AidFTech/AIBus-Universal-Auto-Infotainment-System/Vehicle-Specific/Honda GA-Net II/CAN Bus Translator/PCB/BOM_9th-Gen-Civic-CANslator-BCM.csv

ID | Name | Designator | Footprint | Quantity | Manufacturer Part | Manufacturer | Supplier | Supplier Part | Price
1 | 0.1uF | C1,C2,C3,C4,C6,C7,C11,C19,C20,C31,C32,C33,C35,C36,C37,C38,C44,C51,C53,C58,C59,C60,C61,C70,C72,C78,C79,C85,C89,C91 | C0603 | 30 | 0603B104K101CT | Walsin Technology Corporation | Digi-Key | 1292-1392-1-ND
2 | 1uF | C5,C56,C57 | C0603 | 3 | CC0603KRX5R8BB105 | YAGEO | Digi-Key | 311-1445-1-ND
3 | 560pF | C8,C12,C16,C18,C21,C22,C29,C30 | C0603 | 8 | 06031C561KAT2A | AVX Corporation | Digi-Key | 478-5002-2-ND
4 | 0.1uF | C9,C15,C23,C28 | C0603 | 4 | 0603B104K101CT | Walsin Technology Corporation | Digi-Key | 1292-1392-2-ND
5 | 22pF | C10,C13,C14,C17,C24,C25,C26,C27 | C0603 | 8 | 0603N220F500CT | Walsin Technology Corporation | Digi-Key | 1292-1500-2-ND
6 | 47uF | C34,C90 | C1206 | 2 | GRM31CR61E476ME44K | Murata Electronics | Digi-Key | 490-GRM31CR61E476ME44KCT-ND
7 | 0.1u | C39,C49,C50,C75,C82 | C0603 | 5 | 06035C104JAT2A | KYOCERA AVX | Digi-Key | 478-5778-1-ND
8 | 10u | C40,C41,C48,C65,C66,C73,C74,C80,C81 | C0805 | 9 | CL21A106KAYNNNG | Samsung Electro-Mechanics | Digi-Key | 1276-6454-1-ND
9 | 22u | C42,C43,C63,C64,C76,C77,C83,C84 | C1210 | 8 | CL32B226KAJNFNE | Samsung Electro-Mechanics | Digi-Key | 1276-3391-1-ND
10 | 10u | C45 | CAP-D5.0-F2.0 | 1 | ECA-1HM100I | Panasonic Electronic Components | Digi-Key | P10425CT-ND
11 | 100n | C46,C62 | C0603 | 2 | 06035C104JAT2A | KYOCERA AVX | Digi-Key | 478-5778-1-ND
12 | 33n | C47 | C0603 | 1 | GCM188R71H333KA55D | Murata Electronics | Digi-Key | 490-8025-1-ND
13 | 1nF | C52 | C0603 | 1 | GRM1885C1H102JA01D | Murata Electronics | Digi-Key | 490-1451-1-ND
14 | 18pF | C54,C55 | C0603 | 2 | 712-QSCP251Q180J1GV001TDKR-ND | Johanson Technology Inc. | Digi-Key | 712-QSCP251Q180J1GV001TCT-ND
15 | 470pF | C67,C68 | C0603 | 2 | CL10C471JB8NNNC | Samsung Electro-Mechanics | Digi-Key | 1276-1168-1-ND
16 | 10nF | C69,C71 | C0603 | 2 | KGM15AR71H103KT | KYOCERA AVX | Digi-Key | 478-KGM15AR71H103KTCT-ND
17 | 1u | C86 | C0603 | 1 | CL10A105KB8NNNC | Samsung Electro-Mechanics | Digi-Key | 1276-1860-1-ND
18 | 2.2uF | C87,C88 | C0603 | 2 | C1608X5R1E225K080AB | TDK Corporation | Digi-Key | 445-5964-1-ND
19 | 5V | D1,D18,D24,D32 | SOD-323_L1.7-W1.3-LS2.7-RD-1 | 4 | BZT52C5V1S-TP | Micro Commercial Co | Digi-Key | BZT52C5V1S-TPMSCT-ND
20 | 3.6V | D2 | SOD-323_L1.7-W1.3-LS2.5-FD | 1 | BZX384-B3V6,115 | Nexperia USA Inc. | Digi-Key | 1727-3655-1-ND
21 | SD103AWS-TP | D3,D6,D7,D8,D9,D10,D11,D12,D13,D16,D20,D21,D22,D26,D28,D29,D30,D35 | SOD-323_L1.8-W1.3-LS2.6-FD | 18 | SD103AWS-TP | Micro Commercial Co | Digi-Key | SD103AWSTPMSCT-ND
22 | PESD1CAN-UX-ES | D4,D5,D14,D15 | SOT-323-3_L2.1-W1.3-P1.32-LS2.1-BR | 4 | PESD1CAN | EVVO | Digi-Key | 5272-PESD1CANCT-ND
23 | SK110-AQ | D17 | DO-214AC_L4.3-W2.7-LS5.2-RD | 1 | Z1SMA1 | Diotec Semiconductor | Digi-Key | 4878-Z1SMA1CT-ND
24 | SK54A-LTP | D19,D27,D31,D34 | DO-214AC_L4.3-W2.4-LS4.7-RD | 4 | SK54A-LTP | Micro Commercial Co | Digi-Key | SK54A-LTPMSCT-ND
25 | 18V | D23,D36 | SOD-123_L2.8-W1.8-LS3.7-RD | 2 | BZT52C18-7-F | Diodes Incorporated | Digi-Key | BZT52C18-FDICT-ND
26 | MBR0530-TP | D25 | SOD-123_L2.7-W1.6-LS3.7-RD-1 | 1 | MBR0530-TP | MCC (Micro Commercial Components) | Digi-Key | MBR0530TPMSCT-ND
27 | 10V | D33 | SOD-123_L2.7-W1.6-LS3.7-RD | 1 | BZT52C10-7-F | Diodes Incorporated | Digi-Key | BZT52C10-FDICT-ND
28 | 5A | F1 | FUSE-TH_01530008Z | 1 | 01530008Z | Littelfuse Inc | Digi-Key | F065-ND
29 | 15A | F2 | FUSE-TH_01530008Z | 1 | 01530008Z | Littelfuse Inc | Digi-Key | F065-ND
30 | HDR-F-2.54_1x9 | H1 | HDR-F-2.54_1X9 | 1 | RS1-09-G | Adam Tech | Digi-Key | 2057-RS1-09-G-ND
31 | 1-770967-0 | J1 | CONN-TH_1-770967-0 | 1 | 1-770967-0 | TE Connectivity(泰科电子) | Digi-Key | A32473-ND
32 | MX34020UF1 | J2 | CONN-TH_MX34020UF1 | 1 | MX34020UF1 | JAE Electronics | Digi-Key | 670-2294-ND
33 | MX34024UF1 | J3 | CONN-TH_MX34024UF1 | 1 | MX34024UF1 | JAE Electronics | Digi-Key | 670-2295-ND
34 | S02B-XASS-1(LF)(SN) | J4 | CONN-TH_P2.50_S02B-XASS-1-LF-SN | 1 | S02B-XASS-1(LF)(SN) | JST Sales America Inc. | Digi-Key | 455-S02B-XASS-1-ND
35 | B4B-XH-AM-R(LF)(SN) | J5 | CONN-TH_B4B-XH-AM-LF-SN | 1 | B4B-XH-A | JST Sales America Inc. | Digi-Key | 455-B4B-XH-A-ND
36 | 39301160 | J7 | CONN-TH_39301160 | 1 | 0039301160 | Molex | Digi-Key | WM1358-ND
37 | S06B-XASK-1(LF)(SN) | J10 | CONN-TH_5P-P2.50_S06B-XASK-1-LF-SN | 1 | S06B-XASK-1(LF)(SN) | JST Sales America Inc. | Digi-Key | 455-4091-ND
38 | PPTC032LFBN-RC | J11 | RHDR6W75P254_2X3_812X508X850P | 1 | PPTC032LFBN-RC | Sullins Connector Solutions | Digi-Key | S7071-ND
39 | 53254-0270 | J12 | MOLEX_53254-0270 | 1 | 0532540270 | Molex | Digi-Key | WM18999-ND
40 | S2B-XH-A-BK(LF)(SN) | J13,J14 | CONN-TH_S2B-XH-A-LF-SN | 2 | S2B-XH-A-BK(LF)(SN) | JST | Digi-Key | 455-S2B-XH-A-ND
41 | 0039303035 | J15 | 0039303035 FIXED | 1 | 0039303035 | Molex | Digi-Key | WM18446-ND
42 | 533750210 | J16 | CONN-TH_533750210 | 1 | 533750210 | Molex | Digi-Key | WM3421-ND
43 | 534260610 | J17 | CONN-TH_534260610 | 1 | 534260610 | Molex | Digi-Key | WM3425-ND
44 | 534260310 | J18 | CONN-TH_3P-P2.50_MOLEX_534260310 | 1 | 534260310 | Molex | Digi-Key | WM7586-ND
45 | 178495-1 | J19 | CONN-TH_178495-1 | 1 | 178495-1 | TE Connectivity AMP Connectors | Digi-Key | A106296-ND
46 | 22uH | L1,L2,L14 | IND-SMD_L6.0-W6.0_ASPI-6045S | 3 | ASPI-6045S-220M-T | Abracon LLC | Digi-Key | 535-ASPI-6045S-220M-TCT-ND
47 | 1u | L3 | L0603 | 1 | MAF1608FAD151CT000 | TDK Corporation | Digi-Key | 445-174936-1-ND
48 | 33uH | L10 | IND-SMD_L6.0-W6.0_ASPI-6045S | 1 | SPM7054VT-330M-D | TDK Corporation | Digi-Key | 445-181516-1-ND
49 | DMN67D8L-7 | Q1,Q4,Q5,Q6,Q7,Q16,Q19,Q20,Q22,Q25,Q27,Q28,Q32,Q35,Q36,Q37,Q39,Q40,Q44,Q46,Q49,Q51,Q54,Q55,Q56,Q57,Q58,Q59,Q62 | SOT-23-3_L3.0-W1.7-P0.95-LS2.9-BR | 29 | DMN67D8L-7 | Diodes Incorporated | Digi-Key | DMN67D8L-7DICT-ND
50 | DMN67D8LW-13 | Q2,Q41 | SOT-323-3_L2.2-W1.3-P1.30-LS2.1-BR | 2 | DMN67D8LW-13 | Diodes Incorporated | Digi-Key | DMN67D8LW-13DICT-ND
51 | DMP2120U-7 | Q3,Q17 | SOT-23-3_L2.9-W1.3-P1.90-LS2.4-BR | 2 | DMP2120U-7 | Diodes Incorporated | Digi-Key | DMP2120U-7DICT-ND
52 | BSS169H6327XTSA1 | Q8,Q9,Q10,Q11,Q12,Q13,Q14,Q15 | SOT-23_L2.9-W1.3-P1.90-LS2.4-BR | 8 | BSS169H6327 | Infineon Technologies | Digi-Key | BSS169H6327XTSA1CT-ND
53 | SI2347DS-T1-GE3 | Q18,Q21,Q23,Q24,Q26,Q29,Q30,Q31,Q34,Q38,Q42,Q43,Q47,Q48,Q52,Q53,Q60,Q61 | SOT-23-3_L2.9-W1.3-P1.83-LS2.4-BR-1 | 18 | SI2347DS-T1-GE3 | Vishay Siliconix | Digi-Key | SI2347DS-T1-GE3CT-ND
54 | IRF5305PBF | Q33 | TO-220F-3_L10.2-W4.7-P2.54-L | 1 | IRF5305PBF | Infineon Technologies | Digi-Key | IRF5305PBF-ND
55 | DMN3404L-7 | Q45,Q50 | SOT-23_L2.9-W1.3-P0.95-LS2.4-BR | 2 | DMN3404L-7 | Diodes Incorporated | Digi-Key | DMN3404LDICT-ND
56 | 100k | R1,R2,R3,R6,R8,R9,R11,R12,R16,R49,R50,R53,R54,R61,R62,R73,R74,R76,R86,R90,R91,R92,R127,R131,R132 | R0603 | 25 | RC0603FR-07100KL | YAGEO | Digi-Key | 311-100KHRCT-ND
57 | 10k | R4,R5,R7,R13,R15,R17,R18,R19,R20,R21,R26,R27,R28,R30,R31,R32,R33,R34,R35,R36,R37,R39,R40,R41,R46,R47,R48,R51,R52,R55,R56,R57,R58,R59,R60,R63,R66,R71,R72,R77,R78,R79,R80,R81,R82,R83,R84,R85,R87,R94,R95,R96,R97,R100,R101,R102,R103,R104,R105,R106,R107,R110,R111,R114,R115,R116,R123,R128,R129,R133 | R0603 | 70 | RNCP0603FTD10K0 | Stackpole Electronics Inc | Digi-Key | RNCP0603FTD10K0CT-ND
58 | 470 | R10,R130 | R0603 | 2 | RC0603JR-07470RL | YAGEO | Digi-Key | 311-470GRCT-ND
59 | 1M | R14 | R0603 | 1 | AC0603JR-071ML | YAGEO | Digi-Key | 311-1MLECT-ND
60 | 100 | R22,R23,R24,R25,R29,R38,R42,R43,R44,R45 | R0603 | 10 | CRCW0603100RFKEAHP | Vishay Dale | Digi-Key | 541-100STR-ND
61 | 200k | R64 | R0603 | 1 | AC0603FR-07200KL | YAGEO | Digi-Key | YAG3575CT-ND
62 | 100k | R65 | R0603 | 1 | RC0603JR-10100KL | YAGEO | Digi-Key | YAG2294CT-ND
63 | 21k | R67 | R0603 | 1 | ERJ-3EKF2102V | Panasonic Electronic Components | Digi-Key | P21.0KHCT-ND
64 | 2k | R68,R69 | R0603 | 2 | RT0603BRD072KL | YAGEO | Digi-Key | YAG1626CT-ND
65 | 10M | R70 | R0603 | 1 | RC0603FR-0710ML | YAGEO | Digi-Key | 311-10.0MHRCT-ND
66 | 12k | R75 | R0603 | 1 | RMCF0603FT12K0 | Stackpole Electronics Inc | Digi-Key | RMCF0603FT12K0CT-ND
67 | 9.76k | R88 | R0603 | 1 | RMCF0603FT9K76 | YAGEO | Digi-Key | RMCF0603FT9K76CT-ND
68 | 30.1k | R89 | R0603 | 1 | RMCF0603FT30K1 | YAGEO | Digi-Key | RMCF0603FT30K1CT-ND
69 | 0.01 | R93 | R0603 | 1 | CSM0603FT10L0 | Stackpole Electronics Inc | Digi-Key | CSM0603FT10L0CT-ND
70 | 1k | R98,R99 | R0603 | 2 | RC0603FR-071KL | YAGEO | Digi-Key | 311-1.00KHRCT-ND
71 | 9.1k | R108 | R0603 | 1 | RC0603FR-079K1L | YAGEO | Digi-Key | 311-9.10KHRCT-ND
72 | 1k | R109 | R0603 | 1 | RMCF0603FT1K00 | Stackpole Electronics Inc | Digi-Key | RMCF0603FT1K00CT-ND
73 | 0 | R112,R113 | R0603 | 2 | RC0603JR-070RL | YAGEO | Digi-Key | 311-0.0GRCT-ND
74 | 27 | R117,R118,R119,R120,R121,R122 | R0603 | 6 | RC0603FR-0727RL | YAGEO | Digi-Key | 311-27.0HRCT-ND
75 | 3k | R124 | R0603 | 1 | RT0603BRD073KL | YAGEO | Digi-Key | YAG1657CT-ND
76 | 47k | R125 | R0603 | 1 | RG1608P-473-B-T5 | Susumu | Digi-Key | RG16P47.0KBCT-ND
77 | 16k | R126 | R0603 | 1 | RT0603BRD0716KL | YAGEO | Digi-Key | YAG1546CT-ND
78 | ATMEGA4808-AUR | U1 | TQFP-32_L7.0-W7.0-P0.80-LS9.0-BL | 1 | ATMEGA4808-AUR | Microchip Technology | Digi-Key | 150-ATMEGA4808-AURCT-ND
79 | AP331AWG-7 | U2,U22 | SOT-25-5_L3.0-W1.8-P0.95-LS3.0-BR | 2 | AP331AWG-7 | Diodes Incorporated | Digi-Key | AP331AWGDICT-ND
80 | MCP2561T-E/SN | U3,U6,U9,U10,U13 | SOIC-8_L4.9-W3.9-P1.27-LS6.0-BL-2 | 5 | MCP2561T-E/SN | Microchip Technology | Digi-Key | MCP2561T-E/SNCT-ND
81 | SN74LVC1G14DBVR-MS | U5 | SOT-23-5_L3.0-W1.7-P0.95-LS2.8-BR | 1 | SN74LVC1G14DBVR-MS | Texas Instruments | Digi-Key | 296-11607-1-ND
82 | MCP2515T-I/SO | U7,U8,U11,U12 | SOIC-18_L11.6-W7.5-P1.27-LS10.3-BL | 4 | MCP2515T-I/SO | Microchip Technology | Digi-Key | MCP2515T-I/SOTR-ND
83 | ADG752BRTZ-REEL7 | U15 | SOT-23-6_L2.9-W1.6-P0.95-LS2.8-BL | 1 | ADG752BRTZ-REEL7 | Analog Devices Inc. | Digi-Key | 505-ADG752BRTZ-REEL7CT-ND
84 | MCP23S08-E/SO | U16,U18,U28 | SOIC-18_L11.6-W7.5-P1.27-LS10.3-BL | 3 | MCP23S08-E/SO | Microchip Technology | Digi-Key | MCP23S08-E/SO-ND
85 | MCP3201T-CI/SN | U17,U32 | SOIC-8_L4.9-W3.9-P1.27-LS6.0-BL | 2 | MCP3201T-CI/SN | Microchip Technology | Digi-Key | MCP3201T-CI/SNCT-ND
86 | AP63301WU-7 | U19,U27,U30 | TSOT-23-6_L2.9-W1.6-P0.95-LS2.8-BR | 3 | AP63301WU-7 | Diodes Incorporated | Digi-Key | AP63301WU-7
87 | AP7375-33SA-7 | U20 | SOT-23-3_L2.9-W1.3-P1.90-LS2.4-BR | 1 | AP7375-33SA-7 | Diodes Incorporated | Digi-Key | 31-AP7375-33SA-7CT-ND
88 | USB2513BI-AEZG | U21 | QFN-36_L6.0-W6.0-P0.50-BL-EP | 1 | USB2513BI-AEZG | Microchip Technology | Digi-Key | USB2513B-AEZC-ND
89 | NCS214RSQT2G | U23 | SC-70-6_L2.0-W1.3-P0.65-LS2.1-BL | 1 | NCS214RSQT2G | onsemi | Digi-Key | NCS214RSQT2GOSCT-ND
90 | LM2596T-ADJ/NOPB | U24 | TO-220-5_L10.5-W15.5-P1.70-TL | 1 | LM2596T-ADJ/NOPB | Texas Instruments | Digi-Key | LM2596T-ADJ/NOPB-ND
91 | NA556 | U25 | SOIC-14_L8.7-W3.9-P1.27-LS6.0-BL | 1 | NA556DR | Texas Instruments | Digi-Key | 296-21754-1-ND
92 | MCP4251-104E/SL | U26 | SOIC-14_L8.7-W3.9-P1.27-LS6.0-BL | 1 | MCP4251-104E/SL | Microchip Technology | Digi-Key | MCP4251-104E/SL-ND
93 | SN74LVC2G04DBVR | U29 | SOT-23-6_L2.9-W1.6-P0.95-LS2.8-BR | 1 | SN74LVC2G04DBVR | Texas Instruments | Digi-Key | 296-13261-1-ND
94 | LM2776DBVT | U31 | SOT-23-6_L2.9-W1.6-P0.95-LS2.8-BR | 1 | LM2776DBVT | Texas Instruments | Digi-Key | 296-42300-1-ND
95 | USB-A2VSW6 | USB1 | USB-A-TH_USB-A2VSW6 | 1 | USB-A2VSW6 | On-Shore Technology, Inc. | Digi-Key | On Shore Technology Inc.
96 | USB-A1HSW6 | USB2 | USB-A-TH_USB-A1HSW6 | 1 | USB-A1HSW6 | On Shore Technology Inc. | Digi-Key | ED2989-ND
97 | UJ2-BH-BL1-TH | USB3 | USB-B-TH_GT-USB-2014-CWG1 | 1 | UJ2-BH-BL1-TH | Same Sky (Formerly CUI Devices) | Digi-Key | 102-3999-ND
98 | 16MHz | X1,X2,X3,X4 | HC-49US-SMD_L7.0-W4.1 | 4 | ECS-160-20-3X-EN-TR | ECS Inc. | Digi-Key | XC1793CT-ND
99 | 24MHz | X5 | CRYSTAL-SMD_4P-L2.0-W1.6-BL-B | 1 | XRCGB24M000F3M00R0 | Murata Electronics | Digi-Key | 490-5576-1-ND
100 | TL061IDT | U4,U14 | SOIC-8_L4.9-W3.9-P1.27-LS6.2-BL | 2 | TL061IDT | STMicroelectronics | Digi-Key | 497-4054-1-ND
