AidFTech/AIBus-Universal-Auto-Infotainment-System/Vehicle-Specific/Honda GA-Net II/Audio Source Translator/PCB/BOM_Honda-GA-Net-Translator.csv

ID | Name | Designator | Footprint | Quantity | Manufacturer Part | Manufacturer | Supplier | Supplier Part | Price
1 | 0.1uF | C1,C6,C7,C8,C9,C11,C14,C15,C16,C17,C18,C19,C20,C21,C22,C23,C24,C25,C26,C27,C28,C29,C30,C31,C32,C34,C36,C37,C38,C39,C42,C43,C52,C55,C73 | C0603 | 35 | 0603B104K101CT | Walsin Technology Corporation | Digi-Key | 1292-1392-1-ND
2 | 33n | C2 | C0603 | 1 | GCM188R71H333KA55D | Murata Electronics | Digi-Key | 490-8025-1-ND
3 | 100n | C3 | C0603 | 1 | 06035C104JAT2A | KYOCERA AVX | Digi-Key | 478-5778-1-ND
4 | 10u | C4 | CAP-D5.0-F2.0 | 1 | ECA-1HM100I | Panasonic Electronic Components | Digi-Key | P10425CT-ND
5 | 1uF | C5,C53,C54 | C0603 | 3 | CC0603KRX5R8BB105 | YAGEO | Digi-Key | 311-1445-1-ND
6 | 100u | C10 | CAP-D6.3×F2.5 | 1 | ESK107M025AE3EA | KEMET | Digi-Key | 399-6650-1-ND
7 | 22pF | C12,C13 | C0603 | 2 | 0603N220F500CT | Walsin Technology Corporation | Digi-Key | 1292-1500-2-ND
8 | 10n | C33,C35,C101 | C0603 | 3 | GCM188R72A103KA37D | Murata Electronics | Digi-Key | 490-4781-1-ND
9 | 10nF | C40 | C0603 | 1 | KGM15AR71H103KT | KYOCERA AVX | Digi-Key | 478-KGM15AR71H103KTCT-ND
10 | 470pF | C41 | C0603 | 1 | CL10C471JB8NNNC | Samsung Electro-Mechanics | Digi-Key | 1276-1168-1-ND
11 | 22u | C45,C46,C57,C58,C59,C60,C67,C68 | C1210 | 8 | CL32B226KAJNFNE | Samsung Electro-Mechanics | Digi-Key | 1276-3391-1-ND
12 | 0.1u | C47,C56,C61,C66 | C0603 | 4 | 06035C104JAT2A | KYOCERA AVX | Digi-Key | 478-5778-1-ND
13 | 10u | C48,C49,C50,C51,C62,C63,C64,C65 | C0805 | 8 | CL21A106KAYNNNG | Samsung Electro-Mechanics | Digi-Key | 1276-6454-1-ND
14 | 5.6V | D1 | SOD-123_L2.7-W1.6-LS3.7-RD-A | 1 | MMSZ5232BT1G | onsemi | Digi-Key | MMSZ5232BT1GOSCT-ND
15 | 3.6V | D2,D10 | SOD-123_L2.7-W1.6-LS3.7-RD-A | 2 | MMSZ4685-TP | Micro Commercial Co | Digi-Key | MMSZ4685-TPMSCT-ND
16 | 6.8V | D3,D4 | SOD-123_L2.7-W1.6-LS3.7-RD-A | 2 | MMSZ4692T1G | onsemi | Digi-Key | MMSZ4692T1GOSCT-ND
17 | POWER | D5 | LED-TH_BD5.0-P2.54-FD | 1 | LTL-4233 | Lite-On Inc. | Digi-Key | 160-1130-ND
18 | ACTIVITY | D6 | LED-TH_BD5.0-P2.54-FD | 1 | LTL-4273 | Lite-On Inc. | Digi-Key | 160-1966-ND
19 | SD103AWS-TP | D7,D8,D9,D11,D13,D15,D17,D19,D22,D23,D24,D25,D27 | SOD-323_L1.8-W1.3-LS2.6-FD | 13 | SD103AWS-TP | Micro Commercial Co | Digi-Key | SD103AWSTPMSCT-ND
20 | SK54A-LTP | D12,D14,D16,D18 | DO-214AC_L4.3-W2.4-LS4.7-RD | 4 | SK54A-LTP | Micro Commercial Co | Digi-Key | SK54A-LTPMSCT-ND
21 | 3.6V | D20 | SOD-323_L1.7-W1.3-LS2.5-FD | 1 | BZX384-B3V6,115 | Nexperia USA Inc. | Digi-Key | 1727-3655-1-ND
22 | 5V | D21 | SOD-323_L1.7-W1.3-LS2.7-RD-1 | 1 | BZT52C5V1S-TP | Micro Commercial Co | Digi-Key | BZT52C5V1S-TPMSCT-ND
23 | PROG | D26 | LED0805-RD | 1 | LTST-C171KGKT | Lite-On Inc. | Digi-Key | 160-1426-1-ND
24 | S08B-XADSS-N | J1,J2 | CONN-TH_8P-P2.50_S08B-XADSS-N-LF-SN | 2 | S08B-XADSS-N | JST Sales America Inc. | Digi-Key | 455-S08B-XADSS-N-ND
25 | MX34012NF1_C9900019510 | J3 | CONN-TH_MX34012NF1 | 1 | MX34012NF1 | JAE Electronics | Digi-Key | 670-2285-ND
26 | 53254-0270 | J4 | MOLEX_53254-0270 | 1 | 0532540270 | Molex | Digi-Key | WM18999-ND
27 | HDR-M-2.54_1x8 | J5 | HDR-M-2.54_2X4 | 1 | TSW-104-07-F-D | Samtec Inc. | Digi-Key | SAM8996-ND
28 | 0559350310 | J6 | 0559350310 | 1 | 0559350310 | Molex | Digi-Key | WM12297-ND
29 | 1u | L1,L2,L3,L4,L5,L6,L7,L8,L9 | L0603 | 9 | MAF1608FAD151CT000 | TDK Corporation | Digi-Key | 445-174936-1-ND
30 | 22uH | L12,L13,L14,L15 | IND-SMD_L6.0-W6.0_ASPI-6045S | 4 | ASPI-6045S-220M-T | Abracon LLC | Digi-Key | 535-ASPI-6045S-220M-TCT-ND
31 | DMN67D8L-7 | Q1,Q4,Q6,Q8,Q9 | SOT-23-3_L3.0-W1.7-P0.95-LS2.9-BR | 5 | DMN67D8L-7 | Diodes Incorporated | Digi-Key | DMN67D8L-7DICT-ND
32 | DMN67D8LW-13 | Q2,Q14,Q16,Q18,Q19,Q20,Q21 | SOT-323-3_L2.2-W1.3-P1.30-LS2.1-BR | 7 | DMN67D8LW-13 | Diodes Incorporated | Digi-Key | DMN67D8LW-13DICT-ND
33 | DMP2120U-7 | Q3 | SOT-23-3_L2.9-W1.3-P1.90-LS2.4-BR | 1 | DMP2120U-7 | Diodes Incorporated | Digi-Key | DMP2120U-7DICT-ND
34 | SI2347DS-T1-GE3 | Q5,Q15 | SOT-23-3_L2.9-W1.3-P1.83-LS2.4-BR-1 | 2 | SI2347DS-T1-GE3 | Vishay Siliconix | Digi-Key | SI2347DS-T1-GE3CT-ND
35 | IRF5305PBF | Q7 | TO-220F-3_L10.2-W4.7-P2.54-L | 1 | IRF5305PBF | Infineon Technologies | Digi-Key | IRF5305PBF-ND
36 | 2N7002 | Q17 | SOT-23_L2.9-W1.3-P0.95-LS2.4-BR | 1 | DMN3404L-7 | Diodes Incorporated | Digi-Key | DMN3404LDICT-ND
37 | 10k | R1,R2,R4,R5,R7,R8,R9,R12,R16,R17,R20,R21,R22,R23,R24,R25,R26,R27,R28,R29,R31,R33,R40,R41,R43,R44,R46,R55,R63,R64,R70,R83 | R0603 | 32 | RNCP0603FTD10K0 | Stackpole Electronics Inc | Digi-Key | RNCP0603FTD10K0CT-ND
38 | 47k | R3,R6,R32,R34 | R0603 | 4 | RC0603FR-0747KL | YAGEO | Digi-Key | 311-47.0KHRCT-ND
39 | 100k | R10,R11,R18,R19,R56,R57,R59,R60,R61,R62,R65,R66,R67,R68 | R0603 | 14 | RC0603FR-07100KL | YAGEO | Digi-Key | 311-100KHRCT-ND
40 | 270 | R13,R14,R45 | R0805 | 3 |  |  | Digi-Key | 311-270ARCT-ND
41 | 100 | R15 | R0805 | 1 |  |  | Digi-Key | A126416CT-ND
42 | 2.2k | R30 | R0603 | 1 | RMCF0603FT2K20 | Stackpole Electronics Inc | Digi-Key | RMCF0603FT2K20CT-ND
43 | 1k | R35,R42 | R0603 | 2 | RC0603FR-071KL | YAGEO | Digi-Key | 311-1.00KHRCT-ND
44 | 20k | R36,R48 | R0603 | 2 | RT0603BRD0720KL | YAGEO | Digi-Key | YAG1582CT-ND
45 | 130k | R37,R47 | R0603 | 2 | RT0603BRD07130KL | YAGEO | Digi-Key | YAG1521CT-ND
46 | 150 | R38,R39,R71 | R0603 | 3 | RC0603FR-07150RL | YAGEO | Digi-Key | 311-150HRCT-ND
47 | 16k | R49 | R0603 | 1 | RT0603BRD0716KL | YAGEO | Digi-Key | YAG1546CT-ND
48 | 47k | R50 | R0603 | 1 | RG1608P-473-B-T5 | Susumu | Digi-Key | RG16P47.0KBCT-ND
49 | 3k | R51 | R0603 | 1 | RT0603BRD073KL | YAGEO | Digi-Key | YAG1657CT-ND
50 | 2k | R52,R53 | R0603 | 2 | RT0603BRD072KL | YAGEO | Digi-Key | YAG1626CT-ND
51 | 21k | R54 | R0603 | 1 | ERJ-3EKF2102V | Panasonic Electronic Components | Digi-Key | P21.0KHCT-ND
52 | 1M | R58 | R0603 | 1 | AC0603JR-071ML | YAGEO | Digi-Key | 311-1MLECT-ND
53 | 10M | R69 | R0603 | 1 | RC0603FR-0710ML | YAGEO | Digi-Key | 311-10.0MHRCT-ND
54 | 270 | R85,R86 | R0603 | 2 | RC0603FR-07270RL | YAGEO | Digi-Key | 311-270HRCT-ND
55 | OS102011MS2QN1 | SW1 | SW-TH_OS102011MS2QN1 | 1 | OS102011MS2QN1 | C&K | Digi-Key | CKN9565-ND
56 | ATMEGA1280-16AU | U1 | ATMEGA2560-16AU | 1 | ATMEGA1280-16AU | Microchip Technology | Digi-Key | ATMEGA1280-16AU-ND
57 | MCP2561T-E/SN | U2,U5,U7 | SOIC-8_L4.9-W3.9-P1.27-LS6.0-BL-2 | 3 | MCP2561T-E/SN | Microchip Technology | Digi-Key | MCP2561T-E/SNCT-ND
58 | SN74LVC1G14DBVR-MS | U3 | SOT-23-5_L3.0-W1.7-P0.95-LS2.8-BR | 1 | SN74LVC1G14DBVR-MS | Texas Instruments | Digi-Key | 296-11607-1-ND
59 | 11.2896MHZ | U4 | OSC-SMD_4P-L2.5-W2.0-BL-1 | 1 | KC2520Z11.2896C1KX00 | KYOCERA AVX | Digi-Key | 478-KC2520Z11.2896C1KX00CT-ND
60 | MCP6006UT-E/OT | U10 | SOT-23-5_L3.0-W1.6-P0.95-LS2.8-BL | 1 | MCP6006UT-E/OT | Microchip Technology | Digi-Key | 150-MCP6006UT-E/OTCT-ND
61 | SN74LVC2G14DCKR(UMW) | U11 | SC-70-6_L2.0-W1.3-P0.65-LS2.2-BL | 1 | SN74LVC2G14DCKR | Texas Instruments | Digi-Key | 296-13011-1-ND
62 | SN74LVC2G00DCTR | U12 | SSOP-8_L3.0-W2.8-P0.65-LS4.0-BL-1 | 1 | SN74LVC2G00DCTR | Texas Instruments | Digi-Key | 296-13257-1-ND
63 | SN74LVC1G08DCKR | U13 | SC-70-5_L2.1-W1.3-P0.65-LS2.1-BR | 1 | SN74LVC1G08DCKR | Texas Instruments | Digi-Key | 296-11602-1-ND
64 | DIT4096IPWR | U14 | SSOP-28 | 1 | DIT4096IPWR | Texas Instruments | Digi-Key | 296-DIT4096IPWRCT-ND
65 | 74HCT123D,652 | U15 | SOIC-16_L9.9-W3.9-P1.27-LS6.0-BL | 1 | 74HCT123D,653 | Nexperia USA Inc. | Digi-Key | 1727-7300-1-ND
66 | SN74LVC1G14DBVR_C434069 | U16 | SOT-23-5_L3.0-W1.7-P0.95-LS2.8-BR | 1 | SN74LVC1G14DBVR | Texas Instruments | Digi-Key | 296-11607-1-ND
67 | SN74HC595DRG4 | U17,U18 | SOIC-16_L9.9-W3.9-P1.27-LS6.0-BL | 2 | SN74HC595DR | Texas Instruments | Digi-Key | 296-14857-1-ND
68 | CD4029BM | U19 | SOIC-16_L9.9-W3.9-P1.27-LS6.0-BL | 1 | CD4029BM96 | Texas Instruments | Digi-Key | 296-38054-1-ND
69 | MCP4251-104E/SL | U20 | SOIC-14_L8.7-W3.9-P1.27-LS6.0-BL | 1 | MCP4251-104E/SL | Microchip Technology | Digi-Key | MCP4251-104E/SL-ND
70 | PCM1808PWR | U21 | TSSOP-14_L5.0-W4.4-P0.65-LS6.4-BL | 1 | PCM1808PWR | Texas Instruments | Digi-Key | 296-26307-1-ND
71 | NE555DR-CN | U22 | SOP-8_L5.0-W4.0-P1.27-LS6.0-BL | 1 | NE555DR-CN | Texas Instruments | Digi-Key | 296-6501-1-ND
72 | AP331AWG-7 | U23 | SOT-25-5_L3.0-W1.8-P0.95-LS3.0-BR | 1 | AP331AWG-7 | Diodes Incorporated | Digi-Key | AP331AWGDICT-ND
73 | D-AS321KTR-G1 | U24 | SOT-23-5_L2.9-W1.6-P0.95-LS2.8-BL | 1 | AS321KTR-G1 | Diodes Incorporated | Digi-Key | AS321KTR-G1DICT-ND
74 | AP63301WU-7 | U25,U26 | TSOT-23-6_L2.9-W1.6-P0.95-LS2.8-BR | 2 | AP63301WU-7 | DIODES(美台) | Digi-Key | AP63301WU-7
75 | AP63301WU-7 | U27,U28 | TSOT-23-6_L2.9-W1.6-P0.95-LS2.8-BR | 2 | AP63301WU-7 | Diodes Incorporated | Digi-Key | AP63301WU-7
76 | TC4W66FU,LF | U30 | SSOP-8_L2.9-W2.8-P0.65-LS4.0-BL | 1 | TC4W66FU,LF | Toshiba Semiconductor and Storage | Digi-Key | TC4W66FULFCT-ND
77 | 16MHz | X1 | HC-49US-SMD_L7.0-W4.1 | 1 | ECS-160-20-3X-EN-TR | ECS Inc. | Digi-Key | XC1793CT-ND
78 | TL061IDT | U6 | SOIC-8_L4.9-W3.9-P1.27-LS6.2-BL | 1 | TL061IDT | STMicroelectronics | Digi-Key | 497-4054-1-ND
79 | LM2904BAQDRQ1 | U8 | SOIC-8_L4.9-W3.9-P1.27-LS6.0-BL | 1 | LM2904BIDR | Texas Instruments | Digi-Key | 296-LM2904BIDRCT-ND
80 | TL072IDR(UMW) | U9 | SOIC-8_L4.9-W3.9-P1.27-LS6.0-BL | 1 | TL072IDR | Texas Instruments | Digi-Key | 296-7194-1-ND
81 | LM6172IM | U29 | SOIC-8_L5.0-W4.0-P1.27-LS6.0-BL | 1 | LM6172IMX/NOPB | Texas Instruments | Digi-Key | LM6172IMX/NOPBCT-ND
