AidFTech/AIBus-Universal-Auto-Infotainment-System/Vehicle-Specific/Honda GA-Net II/2006-2011 Navigation Screen/PCB/BOM_8th-gen-Civic-Navigation-Screen-AIBT-Front.csv

ID | Name | Designator | Footprint | Quantity | Manufacturer Part | Manufacturer | Supplier | Supplier Part | Price
1 | 10k | R21,R17,R18,R19,R16,R14,R15,R13,R9,R10,R6,R7,R8,R1,R2,R4 | R0603 | 16 | RNCP0603FTD10K0 | Stackpole Electronics Inc | Digi-Key | RNCP0603FTD10K0CT-ND
2 | SD103AWS-TP | D7,D6 | SOD-323_L1.8-W1.3-LS2.6-FD | 2 | SD103AWS-TP | Micro Commercial Co | Digi-Key | SD103AWSTPMSCT-ND
3 | SI2347DS-T1-GE3 | Q11 | SOT-23-3_L2.9-W1.3-P1.83-LS2.4-BR-1 | 1 | SI2347DS-T1-GE3 | Vishay Siliconix | Digi-Key | SI2347DS-T1-GE3CT-ND
4 | DMN67D8LW-13 | Q12,Q1,Q3,Q4,Q6,Q10 | SOT-23_L2.9-W1.3-P0.95-LS2.4-BR | 6 | DMN67D8LW-13 | Diodes Incorporated | Digi-Key | DMN67D8LW-13DICT-ND
5 | 12k | R20 | R0603 | 1 | RMCF0603FT12K0 | Stackpole Electronics Inc | Digi-Key | RMCF0603FT12K0CT-ND
6 | LM393PSRG4 | U17 | SOIC-8_L6.2-W5.3-P1.27-LS8.0-BL | 1 | LM393DR | Texas Instruments | Digi-Key | 296-1015-1-ND
7 | SN74LVC1G08DBVR | U18 | SOT-23-5_L3.0-W1.7-P0.95-LS2.8-BR | 1 | SN74LVC1G08DBVR | Texas Instruments | Digi-Key | 296-11601-1-ND
8 | 100n | C32,C27,C28,C29,C30,C31,C1,C2,C3,C7,C12,C20,C21,C22,C25,C26 | C0603 | 16 | 06035C104JAT2A | KYOCERA AVX | Digi-Key | 478-5778-1-ND
9 | CD40107BM96 | U15 | SOIC-8_L4.9-W3.9-P1.27-LS6.0-BL | 1 | CD40107BM96 | Texas Instruments | Digi-Key | 296-31481-1-ND
10 | SN74LVC2G14DCKR_C19829677 | U16,U10 | SOT-363_L2.1-W1.3-P0.65-LS2.2-BL | 2 | SN74LVC2G14DCKR | Texas Instruments | Digi-Key | 296-13011-1-ND
11 | CD4029BM | U11,U13 | SOIC-16_L9.9-W3.9-P1.27-LS6.0-BL | 2 | CD4029BM96 | Texas Instruments | Digi-Key | 296-38054-1-ND
12 | MCP23S08-E/SO | U12,U2,U3,U4 | SOIC-18_L11.6-W7.5-P1.27-LS10.3-BL | 4 | MCP23S08-E/SO | Microchip Technology | Digi-Key | MCP23S08-E/SO-ND
13 | SN74LVC1G32DCKRE4 | U14 | SC-70-5_L2.0-W1.3-P0.65-LS2.1-BR | 1 | SN74LVC1G32DCKR | Texas Instruments | Digi-Key | 296-9848-1-ND
14 | 22pF | C4,C5 | C0603 | 2 | 0603N220F500CT | Walsin Technology Corporation | Digi-Key | 1292-1500-2-ND
15 | 0.1uF | C6 | C0603 | 1 | 0603B104K101CT | Walsin Technology Corporation | Digi-Key | 1292-1392-2-ND
16 | 0.1u | C13 | C0603 | 1 | 06035C104JAT2A | KYOCERA AVX | Digi-Key | 478-5778-1-ND
17 | 10n | C23,C24 | C0603 | 2 | GCM188R72A103KA37D | Murata Electronics | Digi-Key | 490-4781-1-ND
18 | 62684-502100AHLF | FPC2 | 62684-502100AHLF | 1 | 62684-502100AHLF | Amphenol ICC (FCI) | Digi-Key | 609-62684-502100AHLFCT-ND
19 | 100k | R11,R12 | R0603 | 2 | RC0603FR-07100KL | YAGEO | Digi-Key | 311-100KHRCT-ND
20 | SN74LVC2G74DCURE4 | U8 | VSSOP-8_L2.3-W2.0-P0.50-LS3.1-BL | 1 | SN74LVC2G74DCUR | Texas Instruments | Digi-Key | 296-12755-1-ND
21 | SN74LVC2G08DCURE4 | U9 | VSSOP-8_L2.1-W2.4-P0.50-LS3.2-BR | 1 | SN74LVC2G08DCUR | Texas Instruments | Digi-Key | 296-13264-1-ND
22 | 91k | R3 | R0603 | 1 | RC0603FR-0791KL | YAGEO | Digi-Key | 311-91.0KHRCT-ND
23 | 7.5k | R5 | R0603 | 1 | RQ73C1J7K5BTD | TE Connectivity Passive Product | Digi-Key | A139653CT-ND
24 | 22uH | L1 | IND-SMD_L6.0-W6.0_ASPI-6045S | 1 | ASPI-6045S-220M-T | Abracon LLC | Digi-Key | 535-ASPI-6045S-220M-TCT-ND
25 | HLE-104-02-F-DV-BE-K-TR | J1 | HDR-SMD_8P-P2.54-V-F-R2-C4-S7.1 | 1 | HLE-104-02-F-DV-BE-K-TR | Samtec Inc. | Digi-Key | 612-HLE-104-02-F-DV-BE-K-TRCT-ND
26 | 6871XX183622_687110183622 | J3,J5 | 687110149022 | 2 | 687110149022 | Würth Elektronik | Digi-Key | 732-5996-1-ND
27 | 10u | C8,C9 | C0805 | 2 | CL21A106KAYNNNG | Samsung Electro-Mechanics | Digi-Key | 1276-6454-1-ND
28 | 22u | C10,C11,C14,C15,C16,C17,C18,C19 | C1210 | 8 | CL32B226KAJNFNE | Samsung Electro-Mechanics | Digi-Key | 1276-3391-1-ND
29 | SK54A-LTP | D1 | DO-214AC_L4.3-W2.4-LS4.7-RD | 1 | SK54A-LTP | Micro Commercial Co | Digi-Key | SK54A-LTPMSCT-ND
30 | BZT52C5V1S-TP | D2 | SOD-323_L1.8-W1.3-LS2.5-RD | 1 | BZT52C5V1S-TP | Micro Commercial Co | Digi-Key | BZT52C5V1S-TPMSCT-ND
31 | 12V | D3 | SOD-123_L2.7-W1.6-LS3.7-RD-A | 1 | BZT52C12-TP | Micro Commercial Co | Digi-Key | BZT52C12-TPMSCT-ND
32 | 3.6V | D4 | SOD-123_L2.7-W1.6-LS3.7-RD-A | 1 | MMSZ4685-TP | Micro Commercial Co | Digi-Key | MMSZ4685-TPMSCT-ND
33 | 5.6V | D5 | SOD-123_L2.7-W1.6-LS3.7-RD-A | 1 | MMSZ5232BT1G | onsemi | Digi-Key | MMSZ5232BT1GOSCT-ND
34 | FH28-60S-0.5SH(05) | FPC1 | FFC-SMD_60P-P0.50_FH28H-60S-0.5SH | 1 | FH28-60S-0.5SH(05) | Hirose Electric Co Ltd | Digi-Key | HFV160CT-ND
35 | 6871XX183622_687120183622 | J2 | 687120183622 | 1 | 687120183622 | Würth Elektronik | Digi-Key | 732-11341-1-ND
36 | SM02B-BHSS-1-TB | J4 | CONN-SMD_SM02B-BHSS-1-TB | 1 | SM02B-BHSS-1-TB(LF)(SN) | JST Sales America Inc. | Digi-Key | 455-2876-1-ND
37 | TP0610K-T1-E3 | Q2,Q5,Q7,Q8,Q9 | SOT-23-3_L2.9-W1.3-P1.83-LS2.4-BR-1 | 5 | TP0610K-T1-E3 | Vishay Siliconix | Digi-Key | TP0610K-T1-E3CT-ND
38 | ATMEGA328P-15AZ | U1 | TQFP-32_L7.0-W7.0-P0.80-LS9.0-BL | 1 | ATMEGA328P-15AZ | Microchip Technology | Digi-Key | ATMEGA328P-AUR
39 | SN74LVC1G32DCKRG4 | U5 | SC-70-5_L2.0-W1.3-P0.65-LS2.1-BR | 1 | SN74LVC1G32DCKRG4 | Texas Instruments | Digi-Key | 296-9848-1-ND
40 | SN74LVC1G14DCKR_C5279049 | U6 | SC-70-5_L2.0-W1.3-P0.65-LS2.1-BR | 1 | SN74LVC1G14DCKR | Texas Instruments | Digi-Key | 296-11608-1-ND
41 | AP63301WU-7 | U7 | TSOT-23-6_L2.9-W1.6-P0.95-LS2.8-BR | 1 | AP63301WU-7 | DIODES(美台) | Digi-Key | AP63301WU-7
42 | 16MHz | X1 | HC-49US-SMD_L7.0-W4.1 | 1 | ECS-160-20-3X-EN-TR | ECS Inc. | Digi-Key | XC1793CT-ND
