AidFTech/AIBus-Universal-Auto-Infotainment-System/Vehicle-Specific/Honda GA-Net II/2006-2011 Navigation Screen/PCB/BOM_8th-gen-Civic-Navigation-Screen-AIBT-Base.csv

ID | Name | Designator | Quantity | Manufacturer Part | Manufacturer | Supplier | Supplier Part
1 | 0.1u | C1,C16,C22,C23,C26,C34 | 6 | 06035C104JAT2A | KYOCERA AVX | Digi-Key | 478-5778-1-ND
2 | 22u | C2,C10,C11,C24,C25,C35,C36 | 7 | CL32B226KAJNFNE | Samsung Electro-Mechanics | Digi-Key | 1276-3391-1-ND
3 | 10n | C3,C15 | 2 | GCM188R72A103KA37D | Murata Electronics | Digi-Key | 490-4781-1-ND
4 | 0.1uF | C4,C5,C6,C7,C12,C14,C29,C30,C31,C32,C37,C38,C39 | 13 | 0603B104K101CT | Walsin Technology Corporation | Digi-Key | 1292-1392-1-ND
5 | 10u | C8,C9,C20,C27,C28,C33 | 6 | CL21A106KAYNNNG | Samsung Electro-Mechanics | Digi-Key | 1276-6454-1-ND
6 | 2.2n | C13 | 1 | GCM1885C1H222JA16D | Murata Electronics | Digi-Key | 490-4968-1-ND
7 | 4.7u | C17 | 1 | 860020472001 | Würth Elektronik | Digi-Key | 732-8818-1-ND
8 | 100u | C18,C19,C21 | 3 | ESK107M025AE3EA | KEMET | Digi-Key | 399-6650-1-ND
9 | 10u | C40 | 1 | ECA-1HM100I | Panasonic Electronic Components | Digi-Key | P10425CT-ND
10 | 100n | C41 | 1 | 06035C104JAT2A | KYOCERA AVX | Digi-Key | 478-5778-1-ND
11 | 1u | C42 | 1 | CL10A105KB8NNNC | Samsung Electro-Mechanics | Digi-Key | 1276-1860-1-ND
12 | SK54A-LTP | D1,D2,D3,D8 | 4 | SK54A-LTP | Micro Commercial Co | Digi-Key | SK54A-LTPMSCT-ND
13 | SD103AWS-TP | D4,D6,D9 | 3 | SD103AWS-TP | Micro Commercial Co | Digi-Key | SD103AWSTPMSCT-ND
14 | SMBJ6.5CA-13-F | D5 | 1 | SMBJ6.5CA-13-F | Diodes Incorporated | Digi-Key | SMBJ6.5CA-FDICT-ND
15 | S1G | D7 | 1 | S1G | SMC Diode Solutions | Digi-Key | 1655-S1GCT-ND
16 | 5-1734839-0 | FPC2 | 1 | 5-1734839-0 | TE Connectivity AMP Connectors | Digi-Key | A100230CT-ND
17 | S20B-PADSS-1(LF)(SN) | J1 | 1 | S20B-PADSS-1(LF)(SN) | JST Sales America Inc. | Digi-Key | 455-S20B-PADSS-1-ND
18 | HDR-M-2.54_1x8 | J2 | 1 | TSW-104-07-F-D | Samtec Inc. | Digi-Key | SAM8996-ND
19 | 10114829-10102LF | J3 | 1 | 10114829-10102LF | Amphenol | Digi-Key | 609-4383-1-ND
20 | 10114829-10104LF | J4 | 1 | 10114829-10104LF | Amphenol ICC (FCI) | Digi-Key | 609-4385-1-ND
21 | 4.7uH | L1 | 1 | ASPI-4030S-4R7M-T | Abracon LLC | Digi-Key | 535-12322-1-ND
22 | 22uH | L2,L7,L8 | 3 | ASPI-6045S-220M-T | Abracon LLC | Digi-Key | 535-ASPI-6045S-220M-TCT-ND
23 | 1u | L3,L4,L5,L6,L9,L11,L12 | 7 | BLM18RK601SN1D | Murata Electronics | Digi-Key | 490-5227-1-ND
24 | 1u | L10 | 1 | BLM18SP102SN1D | Murata Electronics | Digi-Key | 490-BLM18SP102SN1DCT-ND
25 | SI2347DS-T1-GE3 | Q1,Q2,Q5,Q6,Q10,Q11,Q14 | 7 | SI2347DS-T1-GE3 | Vishay Siliconix | Digi-Key | SI2347DS-T1-GE3CT-ND
26 | DMN67D8LW-13 | Q3,Q4,Q12,Q13,Q19,Q20 | 6 | DMN67D8LW-13 | Diodes Incorporated | Digi-Key | DMN67D8LW-13DICT-ND
27 | IRF5305PBF | Q7 | 1 | IRF5305PBF | Infineon Technologies | Digi-Key | IRF5305PBF-ND
28 | DMG2302UK-7-ES | Q15,Q16,Q21 | 3 | DMG2302UK-7 | Diodes Incorporated | Digi-Key | DMG2302UK-7DICT-ND
29 | SI2347DS-T1-GE3 | Q17,Q18 | 2 | DMP2123L-7 | Diodes Incorporated | Digi-Key | DMP2123LDICT-ND
30 | 10k | R1,R2,R4,R7,R8,R9,R38,R45,R46,R49,R52,R54,R56,R57,R58,R59,R60,R62,R63,R64,R65,R66,R69 | 23 | RNCP0603FTD10K0 | Stackpole Electronics Inc | Digi-Key | RNCP0603FTD10K0CT-ND
31 | 110k | R3 | 1 | RC0603FR-07110KL | YAGEO | Digi-Key | 311-110KHRCT-ND
32 | 16k | R5 | 1 | RC0603FR-0716KL | YAGEO | Digi-Key | 311-16.0KHRCT-ND
33 | 124k | R6 | 1 | RC0603FR-07124KL | YAGEO | Digi-Key | 311-124KHRCT-ND
34 | 20k | R6_1 | 1 | RT0603BRD0720KL | YAGEO | Digi-Key | YAG1582CT-ND
35 | 130k | R6_2 | 1 | RT0603BRD07130KL | YAGEO | Digi-Key | YAG1521CT-ND
36 | 33 | R10,R11,R12,R13,R14,R15,R16,R17,R18,R19,R20,R21,R22,R23,R24,R25,R26,R27,R28,R29,R30,R31,R32,R33,R34,R35,R36,R37 | 28 | WR06X330 JTL | Walsin Technology Corporation | Digi-Key | 1292-WR06X330JTLCT-ND
37 | 100 | R39,R40,R41,R42,R43 | 5 | ERJ-3EKF1000V | Panasonic Electronic Components | Digi-Key | P100HCT-ND
38 | 10M | R44 | 1 | RMCF0603FT10M0 | Stackpole Electronics Inc | Digi-Key | RMCF0603FT10M0CT-ND
39 | 1k | R47 | 1 | RC0603FR-071KL | YAGEO | Digi-Key | 311-1.00KHRCT-ND
40 | 34k | R48 | 1 | RC0603FR-0734KL | YAGEO | Digi-Key | 311-34.0KHRCT-ND
41 | 100k | R50,R51,R55 | 3 | RC0603JR-10100KL | YAGEO | Digi-Key | YAG2294CT-ND
42 | 18k | R53 | 1 | RC0603JR-0718KL | YAGEO | Digi-Key | 311-18KGRCT-ND
43 | 115k | R61 | 1 | RC0603FR-07115KL | YAGEO | Digi-Key | 311-115KHRCT-ND
44 | 0.1 | R67 | 1 | KDV08DR100ET | Ohmite | Digi-Key | 273-KDV08DR100ETCT-ND
45 | 20k | R68 | 1 | RQ73C1J20KBTD | TE Connectivity Passive Product | Digi-Key | A140451CT-ND
46 | 30k | R70 | 1 | RR0816P-303-D | Susumu | Digi-Key | RR08P30.0KDCT-ND
47 | 82k | R71 | 1 | RC0603FR-0782KL | YAGEO | Digi-Key | 311-82.0KHRCT-ND
48 | MP1542DK-LF-Z | U1 | 1 | MP1542DK-LF-Z | Monolithic Power Systems Inc. | Digi-Key | 1589-1531-1-ND
49 | TLV1805QDBVRQ1 | U2 | 1 | TLV1805QDBVRQ1 | Texas Instruments | Digi-Key | 296-TLV1805QDBVRQ1CT-ND
50 | SN65LVDS94DGGR | U3 | 1 | SN65LVDS94DGGR | Texas Instruments | Digi-Key | 296-41399-1-ND
51 | ICM7555 | U4 | 1 | ICM7555IBAZ-T | Renesas Electronics Corporation | Digi-Key | ICM7555IBAZ-TCT-ND
52 | MCP2551T-I/SN | U5 | 1 | MCP2551-I/SN | Microchip Technology | Digi-Key | MCP2551-I/SN-ND
53 | SN74LVC1G32DCKR | U6 | 1 | SN74LVC1G32DCKR | Texas Instruments | Digi-Key | 296-9848-1-ND
54 | AP63301WU-7 | U7,U10,U15 | 3 | AP63301WU-7 | DIODES(美台) | Digi-Key | AP63301WU-7
55 | TPS7A24125DBVR | U9 | 1 |  | Texas Instruments | Digi-Key | 296-TPS7A24125DBVRCT-ND
56 | SN74LVC2G02DCUR | U12 | 1 | SN74LVC2G02DCUR | Texas Instruments | Digi-Key | 296-13260-1-ND
57 | SN74LVC2G04DCKR | U13 | 1 | SN74LVC2G04DCKR | Texas Instruments | Digi-Key | 296-13262-1-ND
58 | LM397MF | U14 | 1 | LM397MF | Texas Instruments | Digi-Key | LM397MF/NOPBCT-ND
59 | D-AS321KTR-G1 | U16 | 1 | AS321KTR-G1 | Diodes Incorporated | Digi-Key | AS321KTR-G1DICT-ND
60 | NCS214RSQT2G | U17 | 1 | NCS214RSQT2G | onsemi | Digi-Key | NCS214RSQT2GOSCT-ND
61 | TLV1812QDRQ1 | U8 | 1 | TLV1812QDRQ1 | Texas Instruments | Digi-Key | 296-TLV1812QDRQ1CT-ND
62 | CD4011BM96 | U11 | 1 | CD4011BM96 | Texas Instruments | Digi-Key | 296-14474-1-ND
