AidFTech/AIBus-Universal-Auto-Infotainment-System/Double DIN Screen/CAD/Print Files/Test Print Back.3mf

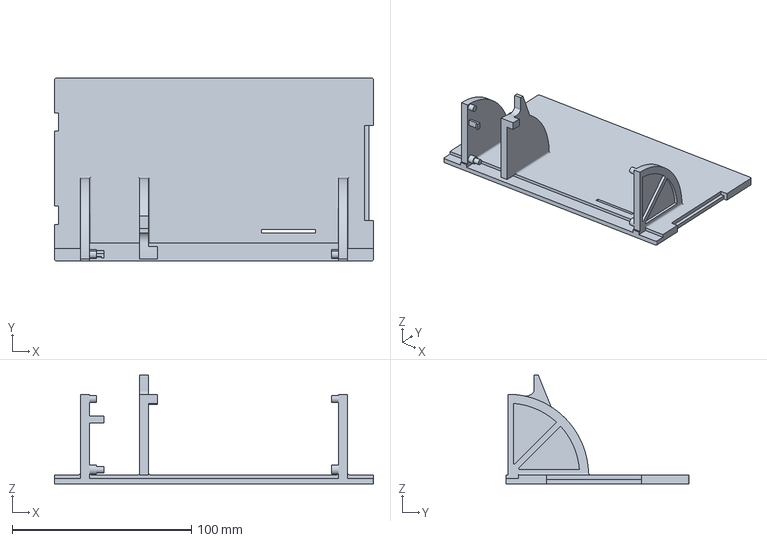
[picture p15: CAD file, 2026-08-22]
Double DIN Screen/CAD/Print Files/Test Print Back.3mf
178.0 x 102.0 x 60.7 mm
