AidFTech/AIBus-Universal-Auto-Infotainment-System/Vehicle-Specific/Honda GA-Net II/Audio Source Translator/CAD/GA-Net Translator Enclosure-GA-Net Translator Lower.stl

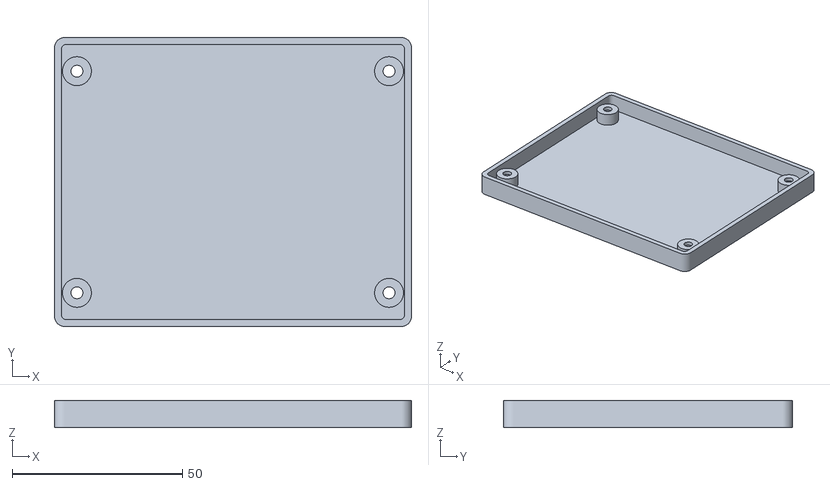
[picture p16: CAD file, 2026-04-12]
Vehicle-Specific/Honda GA-Net II/Audio Source Translator/CAD/GA-Net Translator Enclosure-GA-Net Translator Lower.stl
105.0 x 85.0 x 8.00
