AidFTech/AIBus-Universal-Auto-Infotainment-System/Vehicle-Specific/Honda GA-Net II/CAN Bus Translator/CAD/CANslator Enclosure.FCStd

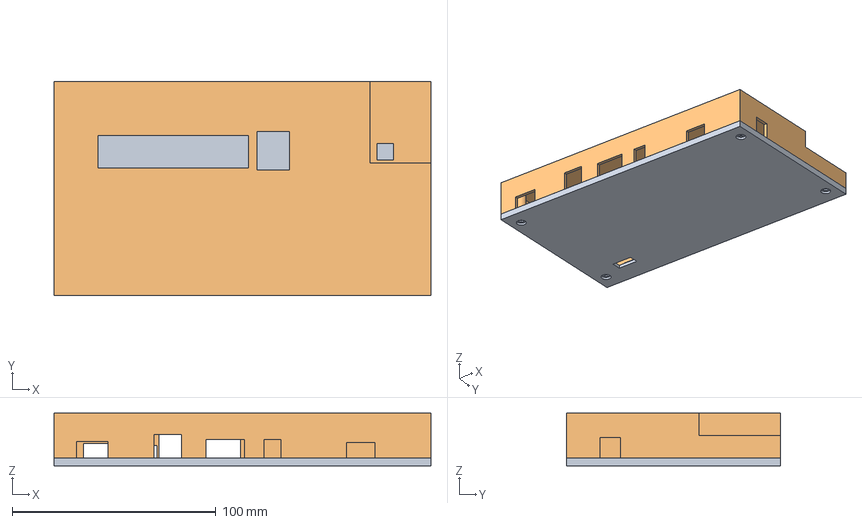
[picture p17: CAD file, 2026-08-22]
Vehicle-Specific/Honda GA-Net II/CAN Bus Translator/CAD/CANslator Enclosure.FCStd
185.0 x 105.0 x 26.0 mm
CANslator Enclsoure Bottom
CANslator Enclosure Top
