AidFTech/AIBus-Universal-Auto-Infotainment-System/Double DIN Screen/CAD/Double DIN Screen Motorized 6 Inch-Right Buttons.3mf

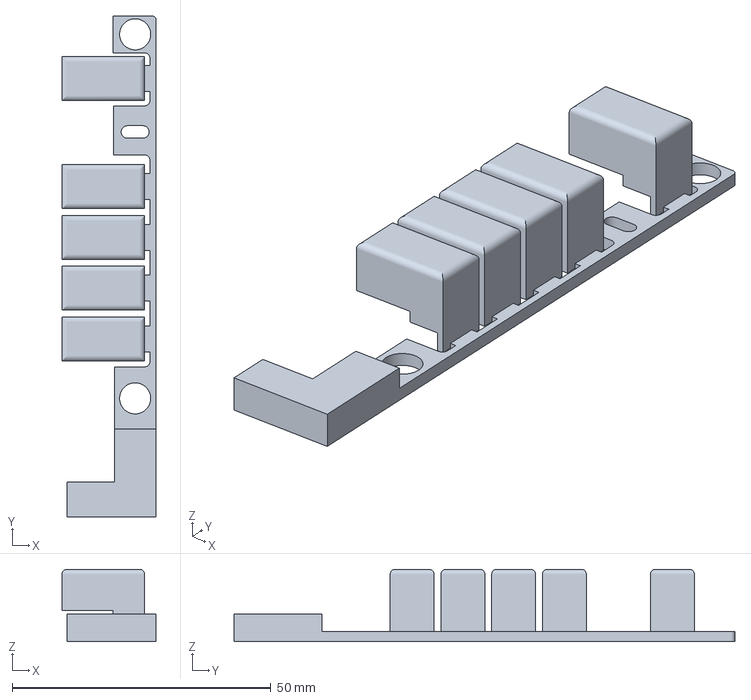
[picture p18: CAD file, 2026-08-22]
Double DIN Screen/CAD/Double DIN Screen Motorized 6 Inch-Right Buttons.3mf
18.2 x 96.8 x 14.0 mm
