AidFTech/AIBus-Universal-Auto-Infotainment-System/Double DIN Screen/CAD/JLC Print Files/Screen Buttons Orca.3mf

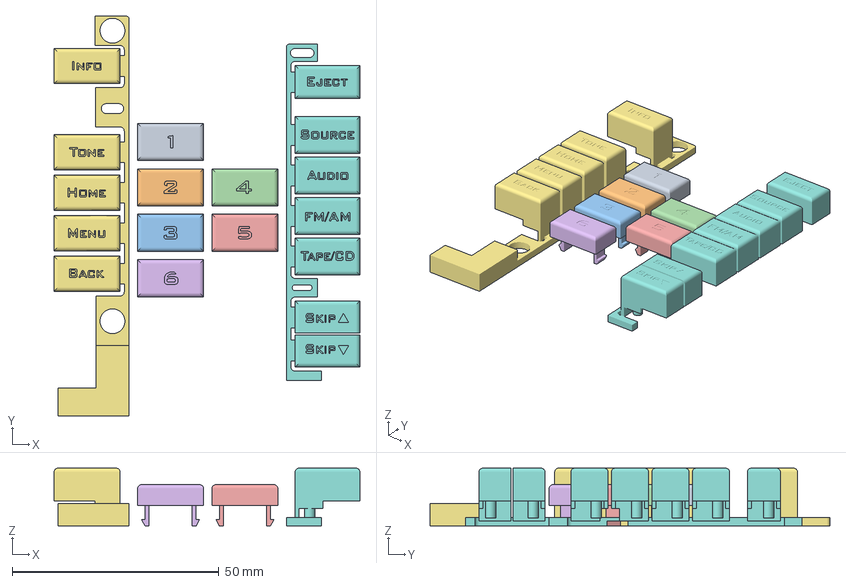
[picture p19: CAD file, 2026-08-22]
Double DIN Screen/CAD/JLC Print Files/Screen Buttons Orca.3mf
74.0 x 96.8 x 14.0 mm
