AidFTech/AIBus-Universal-Auto-Infotainment-System/Double DIN Screen/CAD/Print Files/Test Print Buttons.3mf

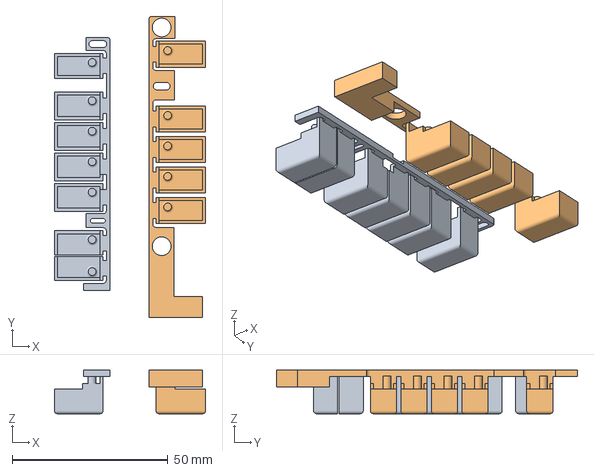
[picture p20: CAD file, 2026-08-22]
Double DIN Screen/CAD/Print Files/Test Print Buttons.3mf
48.6 x 96.8 x 14.0 mm
Double DIN Screen Motorized 6 Inch-Left Buttons
Double DIN Screen Motorized 6 Inch-Right Buttons
