AidFTech/AIBus-Universal-Auto-Infotainment-System/Vehicle-Specific/Honda GA-Net II/CAN Bus Translator/CAD/CANslator Enclosure-CANslator Enclsoure Bottom.3mf

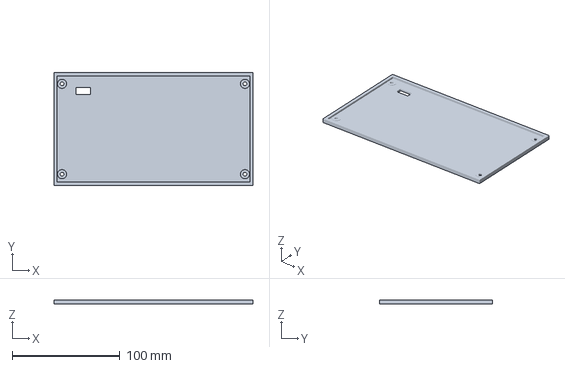
[picture p21: CAD file, 2026-08-22]
Vehicle-Specific/Honda GA-Net II/CAN Bus Translator/CAD/CANslator Enclosure-CANslator Enclsoure Bottom.3mf
185.0 x 105.0 x 4.00 mm
