AidFTech/AIBus-Universal-Auto-Infotainment-System/Double DIN Screen/CAD/Double DIN Screen Motorized 6 Inch-Left Screen Guide.3mf

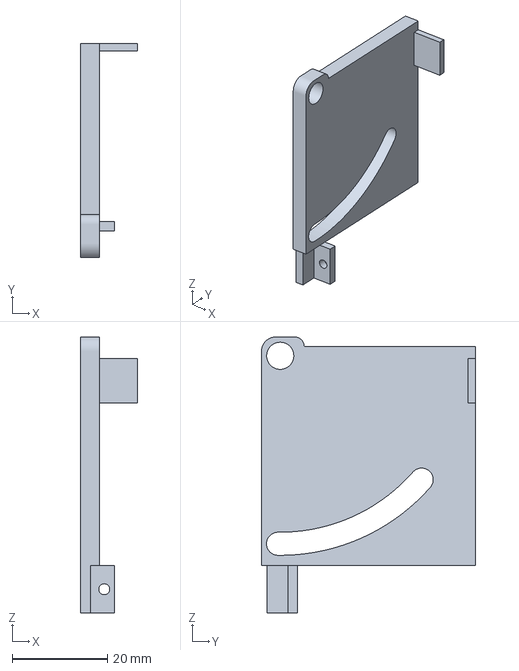
[picture p22: CAD file, 2026-08-22]
Double DIN Screen/CAD/Double DIN Screen Motorized 6 Inch-Left Screen Guide.3mf
12.0 x 45.0 x 58.0 mm
