AidFTech/AIBus-Universal-Auto-Infotainment-System/Double DIN Screen/CAD/JLC Print Files/Screen Buttons Right.3mf

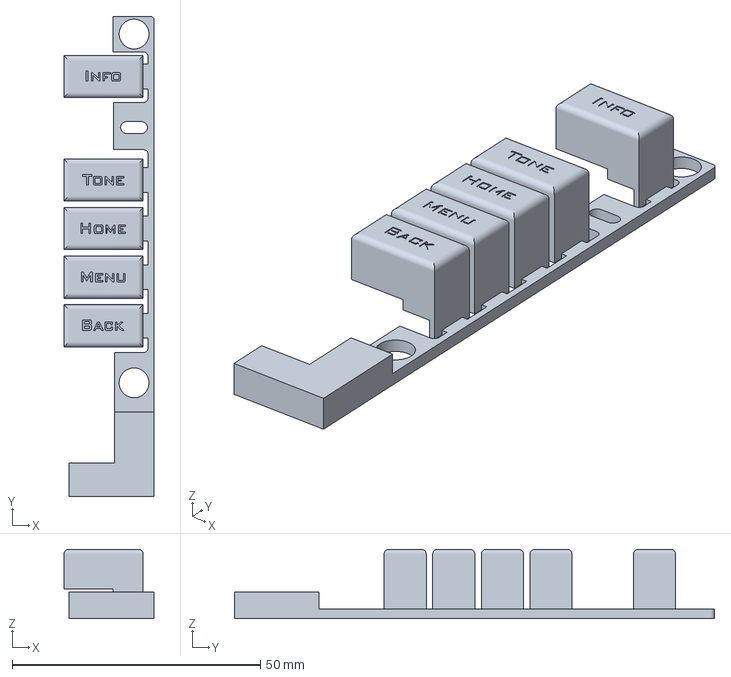
[picture p23: CAD file, 2026-08-22]
Double DIN Screen/CAD/JLC Print Files/Screen Buttons Right.3mf
18.2 x 96.8 x 14.0 mm
