AidFTech/AIBus-Universal-Auto-Infotainment-System/Double DIN Screen/CAD/Print Files/Test Print Function Buttons.3mf

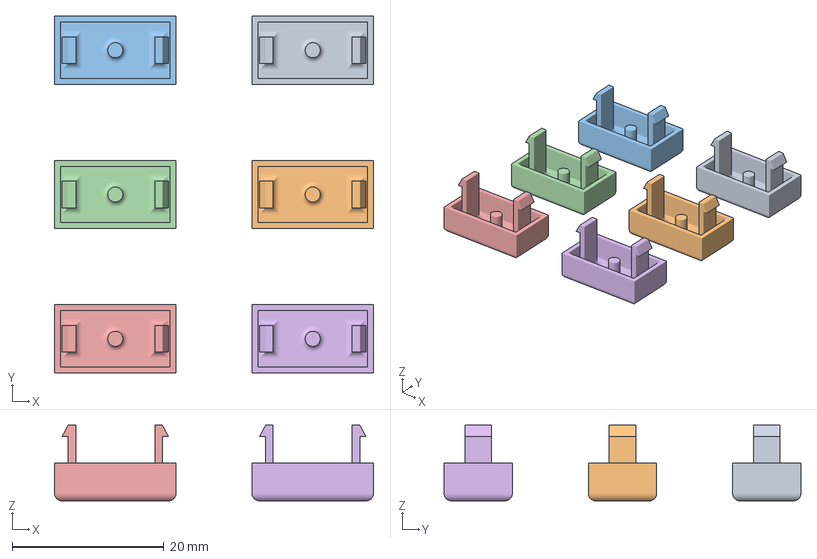
[picture p24: CAD file, 2026-08-22]
Double DIN Screen/CAD/Print Files/Test Print Function Buttons.3mf
42.0 x 47.0 x 10.0 mm
Double DIN Screen Motorized 6 Inch-Preset Button 1
Double DIN Screen Motorized 6 Inch-Preset Button 2
Double DIN Screen Motorized 6 Inch-Preset Button 3
Double DIN Screen Motorized 6 Inch-Preset Button 4
Double DIN Screen Motorized 6 Inch-Preset Button 5
Double DIN Screen Motorized 6 Inch-Preset Button 6
