AidFTech/AIBus-Universal-Auto-Infotainment-System/Double DIN Screen/CAD/Print Files/Test Print Front.3mf

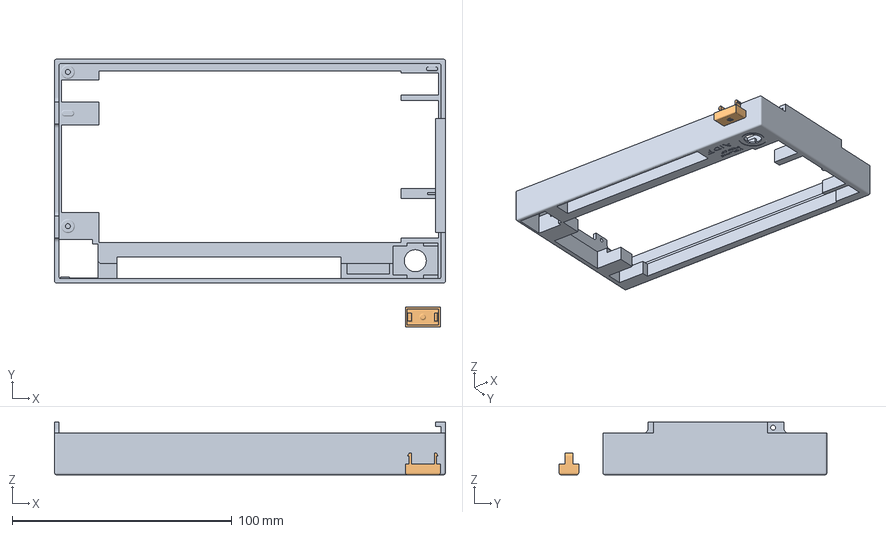
[picture p25: CAD file, 2026-08-22]
Double DIN Screen/CAD/Print Files/Test Print Front.3mf
178.0 x 121.9 x 24.0 mm
Double DIN Screen Motorized 6 Inch-Screen Panel
Double DIN Screen Motorized 6 Inch-Preset Button 5
