AidFTech/AIBus-Universal-Auto-Infotainment-System/Double DIN Screen/CAD/Print Files/Test Print Side Buttons.3mf

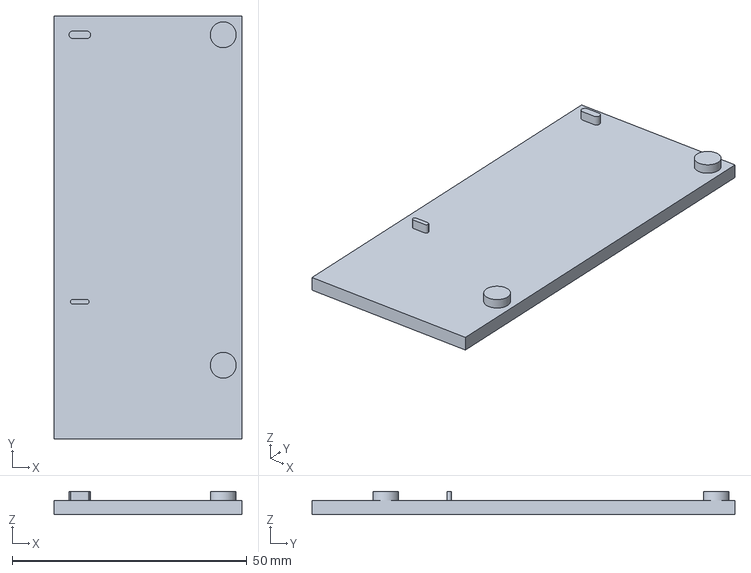
[picture p26: CAD file, 2026-08-22]
Double DIN Screen/CAD/Print Files/Test Print Side Buttons.3mf
40.0 x 90.0 x 5.00 mm
