AidFTech/AIBus-Universal-Auto-Infotainment-System/Double DIN Screen/CAD/Function Button Guide-Function Button Support.3mf

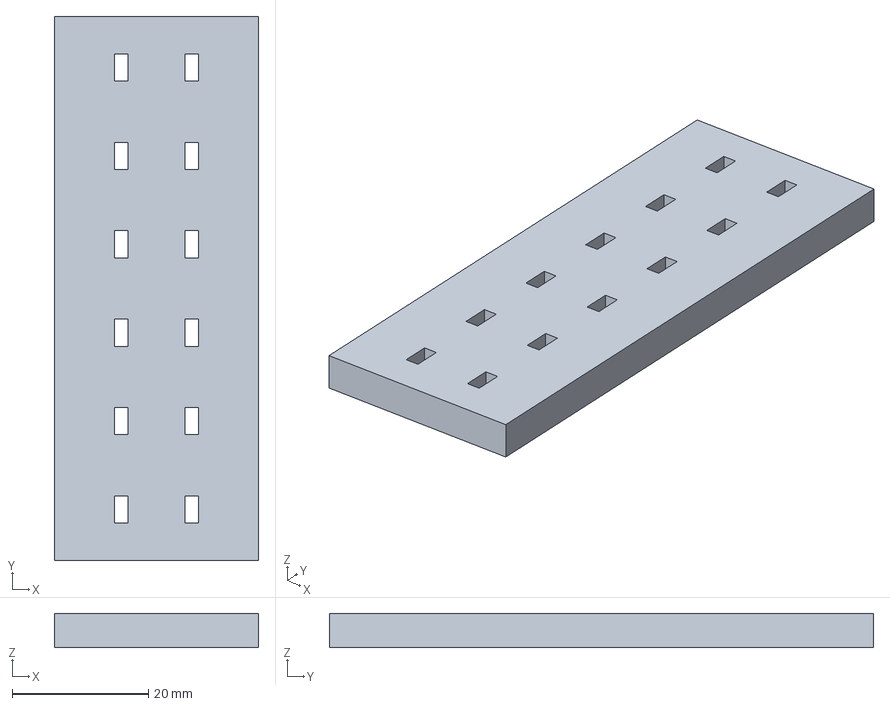
[picture p27: CAD file, 2026-08-22]
Double DIN Screen/CAD/Function Button Guide-Function Button Support.3mf
30.0 x 80.0 x 5.00 mm
