AidFTech/AIBus-Universal-Auto-Infotainment-System/Double DIN Screen/CAD/Double DIN Screen Motorized 6 Inch.FCStd

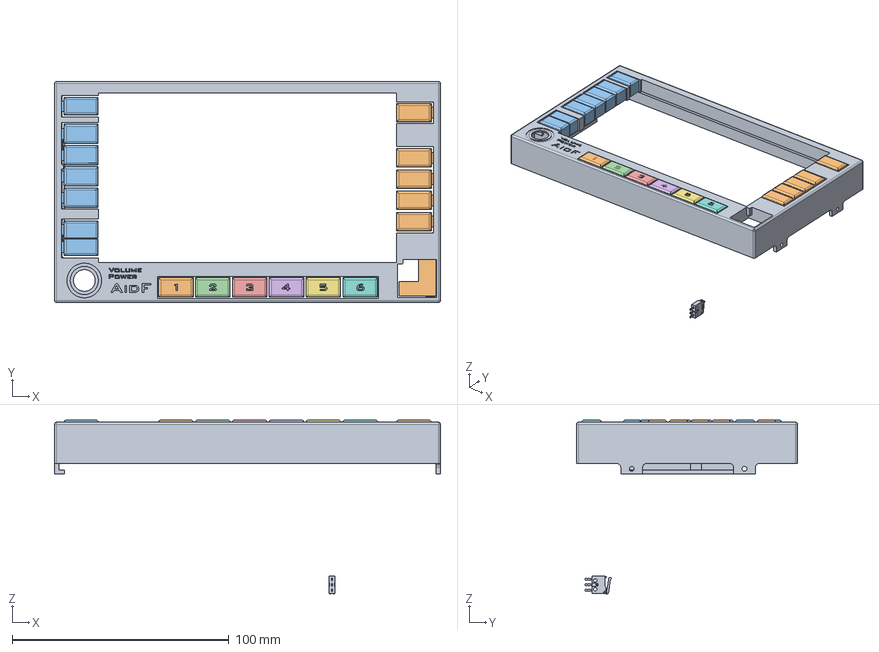
[picture p28: CAD file, 2026-08-22]
Double DIN Screen/CAD/Double DIN Screen Motorized 6 Inch.FCStd
178.0 x 102.0 x 80.2 mm
Screen Panel
Right Buttons
Left Buttons
Preset Button 2
Preset Button 3
Preset Button 4
Preset Button 5
Preset Button 6
P:\E-Switch Secure\3D_MODELS_STP_FORMAT\TS0101F020P.stp
Preset Button 1
