AidFTech/AIBus-Universal-Auto-Infotainment-System/Double DIN Screen/CAD/Double DIN Screen Motorized 6 Inch-Screen Panel.3mf

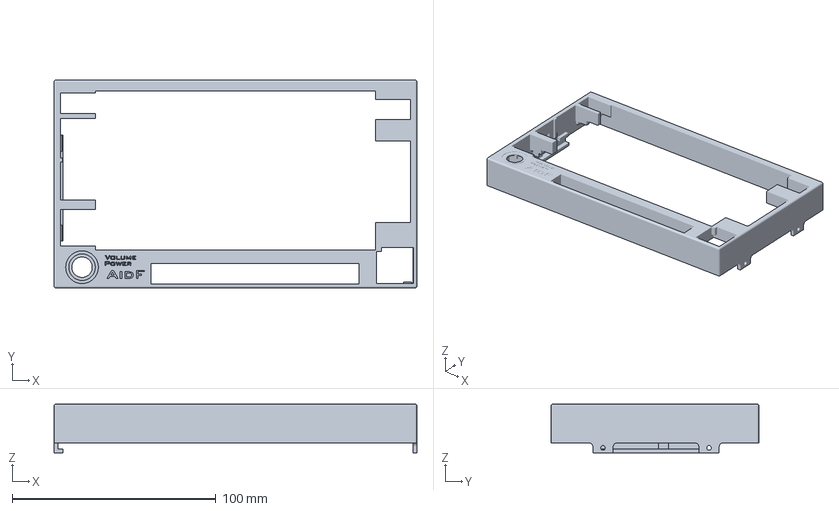
[picture p29: CAD file, 2026-08-22]
Double DIN Screen/CAD/Double DIN Screen Motorized 6 Inch-Screen Panel.3mf
178.0 x 102.0 x 24.0 mm
