AidFTech/AIBus-Universal-Auto-Infotainment-System/Double DIN Screen/CAD/Double DIN Screen Motorized 6 Inch-Nav Toggle Cover.3mf

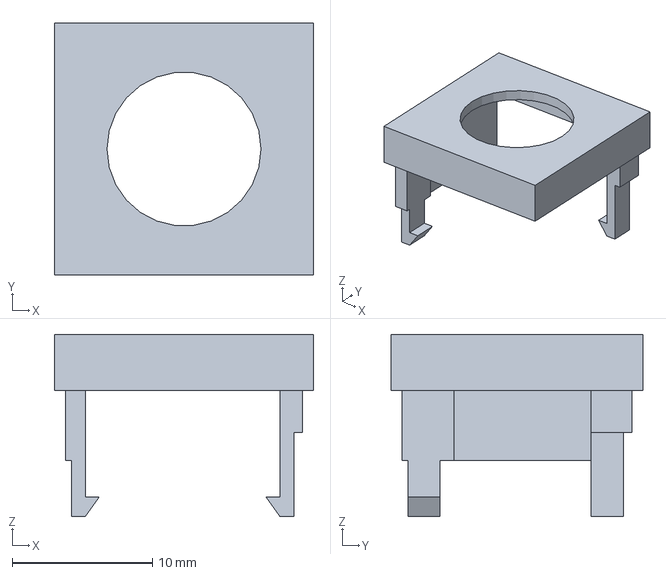
[picture p30: CAD file, 2025-07-30]
Double DIN Screen/CAD/Double DIN Screen Motorized 6 Inch-Nav Toggle Cover.3mf
18.5 x 18.0 x 13.0 mm
