AidFTech/AIBus-Universal-Auto-Infotainment-System/Double DIN Screen/CAD/Double DIN Screen Motorized 6 Inch-Right Screen Guide.3mf

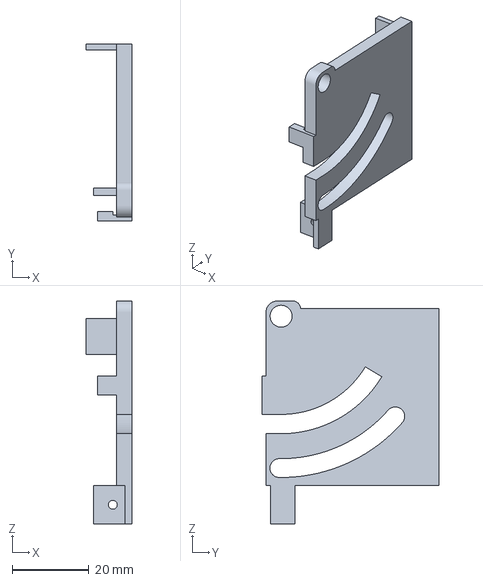
[picture p31: CAD file, 2025-07-30]
Double DIN Screen/CAD/Double DIN Screen Motorized 6 Inch-Right Screen Guide.3mf
12.0 x 46.0 x 58.0 mm
