AidFTech/AIBus-Universal-Auto-Infotainment-System/Double DIN Screen/CAD/Double DIN Screen Motorized 6 Inch-Screen Back Guidepost.3mf

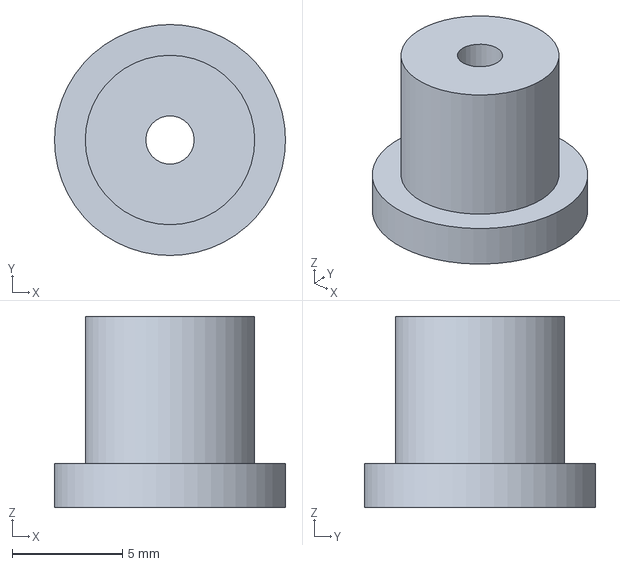
[picture p32: CAD file, 2025-06-24]
Double DIN Screen/CAD/Double DIN Screen Motorized 6 Inch-Screen Back Guidepost.3mf
10.5 x 10.5 x 8.70 mm
