AidFTech/AIBus-Universal-Auto-Infotainment-System/Double DIN Screen/CAD/Double DIN Screen Motorized 6 Inch-Knob.dxf

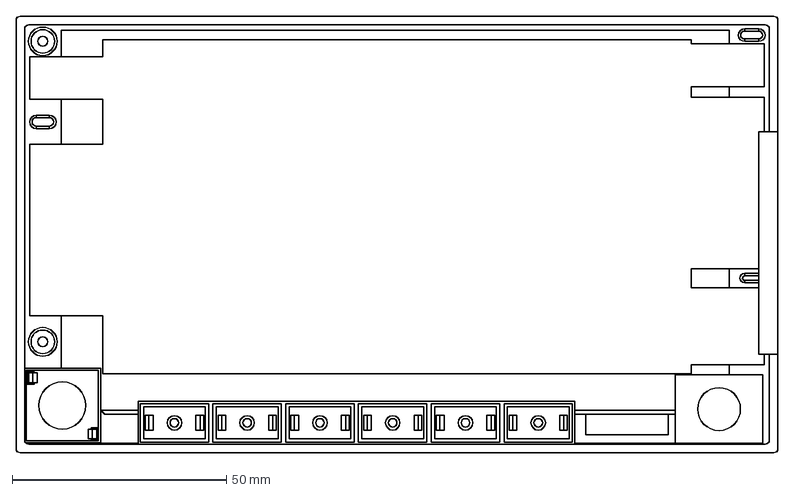
[picture p33: CAD file, 2025-06-24]
Double DIN Screen/CAD/Double DIN Screen Motorized 6 Inch-Knob.dxf
178.0 x 102.0 mm
