AidFTech/AIBus-Universal-Auto-Infotainment-System/Double DIN Screen/CAD/Double DIN Screen Motorized 6 Inch-Top.dxf

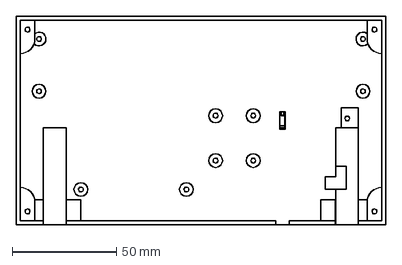
[picture p34: CAD file, 2025-06-24]
Double DIN Screen/CAD/Double DIN Screen Motorized 6 Inch-Top.dxf
177.0 x 100.0 mm
