AidFTech/AIBus-Universal-Auto-Infotainment-System/Double DIN Screen/CAD/RKJXT1F42001.STEP

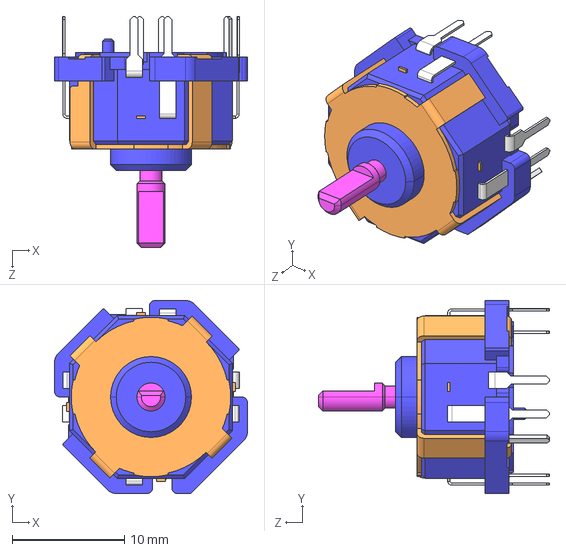
[picture p35: CAD file, 2025-06-05]
Double DIN Screen/CAD/RKJXT1F42001.STEP
17.2 x 17.2 x 20.6 mm
