AidFTech/AIBus-Universal-Auto-Infotainment-System/Double DIN Screen/CAD/PEC11S-929K.STP

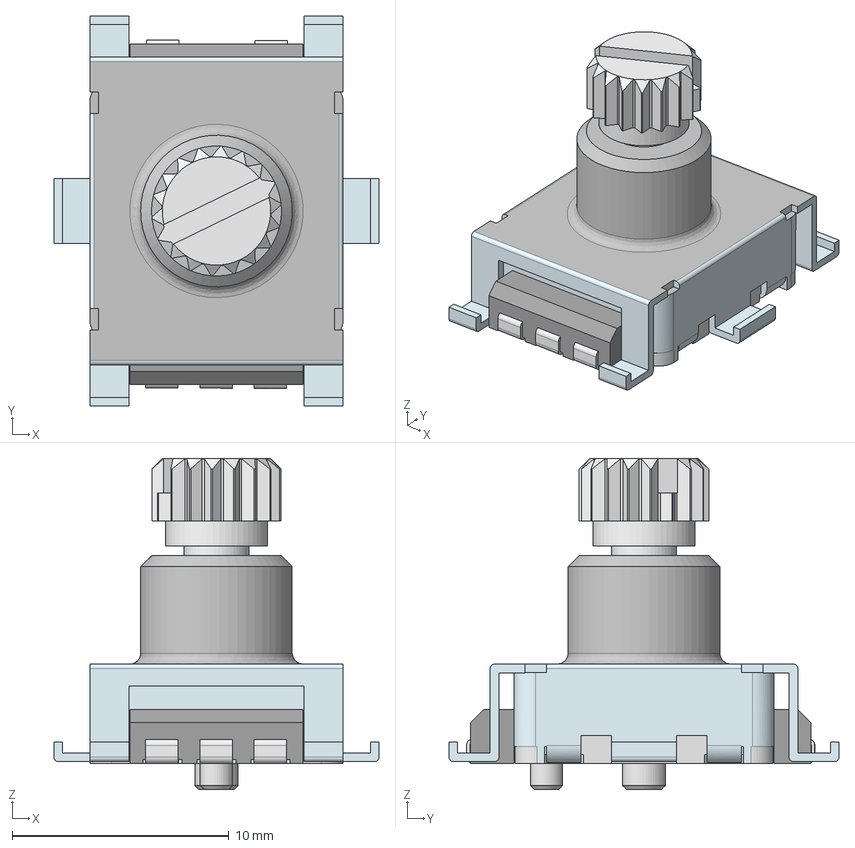
[picture p36: CAD file, 2025-06-05]
Double DIN Screen/CAD/PEC11S-929K.STP
15.0 x 18.0 x 15.3 mm
