AidFTech/AIBus-Universal-Auto-Infotainment-System/Double DIN Screen/CAD/TL1015AFxxxQG.stp

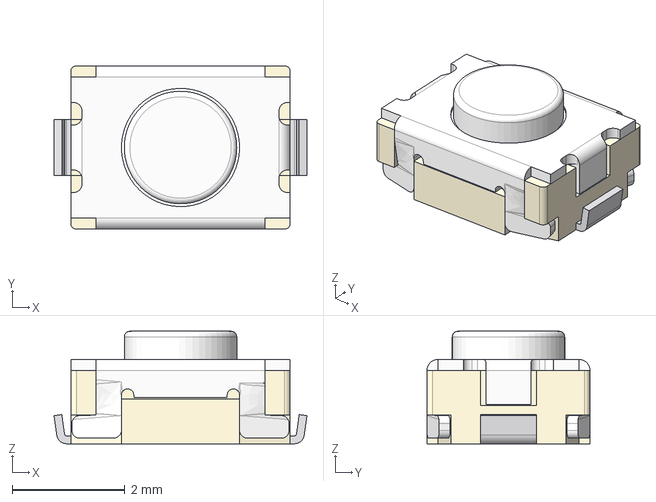
[picture p37: CAD file, 2025-06-05]
Double DIN Screen/CAD/TL1015AFxxxQG.stp
4.50 x 2.90 x 2.00 mm
