AidFTech/AIBus-Universal-Auto-Infotainment-System/Double DIN Screen/CAD/141_TS0101F020P.stp

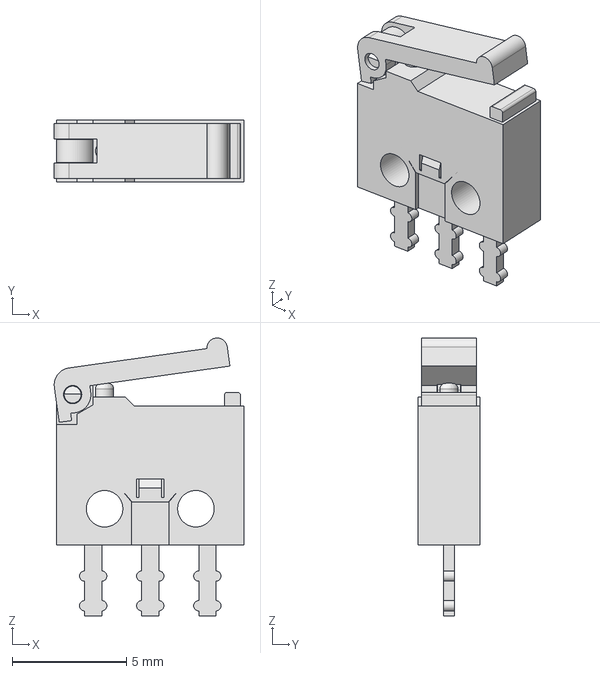
[picture p38: CAD file, 2025-06-05]
Double DIN Screen/CAD/141_TS0101F020P.stp
8.31 x 2.70 x 12.2 mm
