AidFTech/AIBus-Universal-Auto-Infotainment-System/Navigation Computer/Code/AidF_Nav_Computer_Pi/AidF_Nav_Computer_Pi.h

#include <SDL2/SDL_render.h>
#include <stdint.h>
#include <SDL2/SDL.h>
#include <SDL2/SDL_video.h>
#include <SDL2/SDL_ttf.h>
#include <SDL2/SDL_mouse.h>

#include <string>
#include <fstream>
#include <filesystem>
#include <vector>
#include <cstdlib>

#include <pthread.h>

#include "AidF_Color_Profile.h"
#include "Window_Handler.h"
#include "Serial_AIBus_Handler.h"
#include "Ini_Context.h"
#include "Ini_Color_Preset.h"
#include "Saved_Settings.h"

#ifdef RPI_UART
#include <gpiod.h>
#endif

#include "Background/Nav_Background.h"
#include "Background/Nav_Solid_Background.h"
#include "Background/Nav_Gradient_Background.h"

#include "Camera/Camera_Handler.h"

#include "Window/Nav_Window.h"
#include "Window/Audio_Window.h"
#include "Window/Phone_Window.h"
#include "Window/Intro_Window.h"

#include "Window/Main_Menu_Window.h"
#include "Window/Consumption_Window.h"
#include "Window/Settings_Main_Window.h"
#include "Window/Settings_Display_Window.h"

#include "Vehicle_Information/Vehicle_Info_Parameters.h"
#include "Vehicle_Information/Power_Flow_Arrow.h"

#include "Map/Nav_Parameters.h"
#include "Map/Map_Main_Window.h"

#include "Socket/AIBus_Socket.h"
#include "Socket/Video_Socket.h"

#ifndef aidf_nav_computer_pi_h
#define aidf_nav_computer_pi_h

#define DEFAULT_W 800
#define DEFAULT_H 480

#define HEADER_LIMIT_VOLUME 700
#define HEADER_LIMIT_OTHER 2000

#define SOCKET_AIBUS_TEST

#ifdef RPI_UART
#define GPIO_I2S_MCLK 4
#define GPIO_DAC_MUTE 17
#define GPIO_USB_PWR 26
#define GPIO_NAV_MUTE 12
#endif

using namespace std;
using namespace filesystem;

struct FrameParameters {
	int* frame;
	bool* run;
};

struct ElapsedMillis {
	unsigned long time = 0;
	bool* run;
};

using namespace std;

class AidF_Nav_Computer {
public:
	bool running = true;

	#ifdef RPI_UART
	bool test_mode = false; //If true, do not shut the Pi down upon termination.
	#endif

	AidF_Nav_Computer(SDL_Window* window, string port, const uint16_t lw, const uint16_t lh);
	~AidF_Nav_Computer();

	void loop();
	uint16_t getWidth();
	uint16_t getHeight();
	SDL_Renderer* getRenderer();

	AidFColorProfile* getColorProfile();
private:
	bool handleBroadcastMessage(AIData* ai_d);

	void sendPowerOffMessage();

	void setDayNight(const bool night);
	void setMirrorColors();

	void getBackground();
	void setMonitorOn(const bool on);

	uint8_t key_position = 0, door_position = 0;
	bool key_switched_on = false; //True once the key has been cycled on.

	uint16_t lw, lh;
	bool* night;

	bool* canslator_connected, *radio_connected, *mirror_connected;

	SDL_Renderer* renderer;
	SDL_Texture* amirror_texture, *camera_texture;
	AidFColorProfile active_color_profile, day_profile, night_profile;

	SerialAIBusHandler* aibus_handler;

	#ifdef RPI_UART
	gpiod_line *line_nav_mute;
	#endif

	Background* br = nullptr;

	Window_Handler* window_handler;
	AttributeList* attribute_list;

	Audio_Window* audio_window;
	PhoneWindow* phone_window;
	Main_Menu_Window* main_window;
	NavWindow* misc_window;

	CameraHandler* camera_handler;

	pthread_t amirror_socket_thread, abta_socket_thread, frame_thread, timer_thread, amirror_video_thread, camera_video_thread;

	SocketHandlerParameters amirror_socket_parameters, abta_socket_parameters;
	VideoSocketParameters amirror_video_socket_parameters, camera_video_socket_parameters;
	FrameParameters frame_parameters;
	ElapsedMillis elapsed_millis;

	unsigned long aibus_read_time = 0;
	
	bool header_timer_enabled = false;
	unsigned long header_timer = 0;

	bool vol_timer_enabled = false;
	unsigned long vol_timer = 0;

	unsigned long all_ping_timer = 0;
};

void setup(AidF_Nav_Computer* nav_computer);
void loop(AidF_Nav_Computer* nav_computer);

int main(int argc, char* args[]);

void *frameThread(void* frame_v);
void *millisThread(void* millis_v);

#endif
