AidFTech/AIBus-Universal-Auto-Infotainment-System/Vehicle-Specific/Honda GA-Net II/Audio Source Translator/Code/Honda_CD_XM_Trans/src/Honda_IMID_Handler.cpp

#include "Honda_IMID_Handler.h"

HondaIMIDHandler::HondaIMIDHandler(EnIEBusHandler* ie_driver, AIBusHandler* ai_driver, ParameterList* parameter_list) : HondaSourceHandler(ie_driver, ai_driver, parameter_list) {
	this->device_ie_id = IE_ID_IMID;
	this->device_ai_id = ID_IMID_SCR;

	requestor_vec.setStorage(requestor_list, 0);
	ai_cache_vec.setStorage(ai_cache);

	getIMIDSettings(&display_rds, &display_volume, (uint8_t*)&char_count);

	switch(char_count) {
	case CHAR_COUNT_8:
		max_char = 8;
		break;
	case CHAR_COUNT_10:
		max_char = 10;
		break;
	case CHAR_COUNT_12:
		max_char = 12;
		break;
	default:
		break;
	}
}

void HondaIMIDHandler::loop() {
	if(!source_established)
		return;

	if(frequency_change_timer_enabled && frequency_change_timer > FREQUENCY_CHANGE_TIMER) {
		frequency_change_timer_enabled = false;
		writeIMIDRadioMessage(frequency, decimal, preset, stereo_mode);
	}

	if(setting_changed) {
		setting_changed = false;
		setIMIDSettings(display_rds, display_volume, char_count);
	}

	if(parameter_list->power_on && imid_next_source >= 0) {
		if(imid_next_subsource < 0)
			imid_next_subsource = 0;

		if(setIMIDSource(imid_next_source&0xFF, imid_next_subsource&0xFF, true)) {
			imid_next_source = -1;
			imid_next_subsource = -1;
		}
		//TODO: Re-ping the source for data.
	}

	if(parameter_list->power_on && imid_change_timer >= IMID_CHANGE_TIMER_LOCAL && ai_cache_vec.size() > 0) {
		ie_driver->cacheAIBus();
		readAIBusMessage(&ai_cache_vec[0]);
		ai_cache_vec.remove(0);

		imid_change_timer = 0;
	}
}

void HondaIMIDHandler::interpretIMIDMessage(IE_Message* the_message) {
	if(the_message->receiver != IE_ID_RADIO || the_message->sender != IE_ID_IMID)
		return;
		
	bool ack = true;

	if(the_message->l == 2 && the_message->data[0] == 0x80) //Acknowledgement.
		return;
	
	if(the_message->l == 4) { //Handshake message.
		if(the_message->data[0] == 0x1 && the_message->data[1] == 0x1) {
			ack = false;
			sendIEAckMessage(IE_ID_IMID);

			ie_driver->addID(ID_IMID_SCR);

			if(!this->parameter_list->first_imid) {
				this->parameter_list->first_imid = true;

				uint8_t handshake_data[] = {0x0, 0x30};
				IE_Message handshake_msg(sizeof(handshake_data), IE_ID_RADIO, 0x1FF, 0xF, false);
				handshake_msg.refreshIEData(handshake_data);
				
				delay(2);

				ie_driver->sendMessage(&handshake_msg, false, false);
			}
		} else if(the_message->data[0] == 0x5 && the_message->data[2] == 0x3) {
			ack = false;
			sendIEAckMessage(IE_ID_IMID);
			
			delay(2);
			
			const bool handshake_rec = sendHandshakeAckMessage();
			if(!source_established) {
				source_established = handshake_rec;
				
				if(source_established) {
					this->parameter_list->imid_connected = true;
					uint8_t ping_data[] = {0x1};
					AIData ping(sizeof(ping_data), ID_IMID_SCR, ID_RADIO);
					ping.refreshAIData(ping_data);

					ai_driver->writeAIData(&ping, parameter_list->radio_connected);

					ie_driver->addID(ID_IMID_SCR);
					
					writeScreenLayoutMessage();
					if(parameter_list->radio_connected)
						writeVolumeLimitMessage();

					//uint8_t audio_off_data[] = {0x0, 0x0};
					//sendFunctionMessage(ie_driver, true, IE_ID_IMID, audio_off_data, sizeof(audio_off_data));
				}
			}
			
		} 
	} else if(the_message->l >= 7 && the_message->data[0] == 0x22 && the_message->data[1] == 0x11) { //Steering wheel button.
		ack = false;
		sendIEAckMessage(IE_ID_IMID);
		
		const uint8_t ctrl = the_message->data[5];

		uint8_t ai_button_data[] = {0x30, 0x00, 0x00};

		switch(ctrl) {
			case 0x5: //Volume down.
				ai_button_data[1] = 0x6;
				ai_button_data[2] |= 0x2;
				break;
			case 0x4: //Volume up.
				ai_button_data[1] = 0x6;
				ai_button_data[2] |= 0x1;
				break;
			case 0x3: //Seek left.
				ai_button_data[1] = 0x24;
				break;
			case 0x2: //Seek right.
				ai_button_data[1] = 0x25;
				break;
			case 0x1: //Source.
				ai_button_data[1] = 0x23;
				break;
		}

		if(button_held != 0 && button_held != ctrl) {
			uint8_t release_data[] = {0x30, 0x00, 0x80};
			switch(button_held) {
				case 0x5: //Volume down.
					release_data[1] = 0x6;
					release_data[2] |= 0x2;
					break;
				case 0x4: //Volume up.
					release_data[1] = 0x6;
					release_data[2] |= 0x1;
					break;
				case 0x3: //Seek left.
					release_data[1] = 0x24;
					break;
				case 0x2: //Seek right.
					release_data[1] = 0x25;
					break;
				case 0x1: //Source.
					release_data[1] = 0x23;
					break;
			}

			AIData release_msg(sizeof(release_data), ID_STEERING_CTRL, ID_RADIO);
			release_msg.refreshAIData(release_data);
			ai_driver->writeAIData(&release_msg, parameter_list->radio_connected);
		} else if(button_held == ctrl && ctrl != 0) {
			ai_button_data[2] |= 0x40;
		}

		if(ctrl != 0 && button_held != ctrl) {
			AIData button_msg(sizeof(ai_button_data), ID_STEERING_CTRL, ID_RADIO);
			button_msg.refreshAIData(ai_button_data);
			ai_driver->writeAIData(&button_msg, parameter_list->radio_connected);
		}

		button_held = ctrl;
	}

	if(ack)
		sendIEAckMessage(IE_ID_IMID);
}

void HondaIMIDHandler::readAIBusMessage(AIData* the_message) {
	if(the_message->receiver != ID_IMID_SCR)
		return;

	if(!parameter_list->power_on)
		return;

	/*if(cache && imid_change_timer < IMID_CHANGE_TIMER_LOCAL && 
			ai_cache_vec.size() < ai_cache_vec.max_size() &&
			!(the_message->l >= 3 && the_message->data[0] == 0x40 && the_message->data[1] == 0x10) &&
			!(the_message->l >= 3 && the_message->data[0] == 0x62)) {
		ai_driver->sendAcknowledgement(ID_IMID_SCR, the_message->sender);	
		ai_cache_vec.push_back(*the_message);
	}*/

	if(the_message->l >= 3 && the_message->data[0] == 0x4 && the_message->data[1] == 0xE6 && the_message->data[2] == 0x3B) {
		writeScreenLayoutMessage(the_message->sender);

		bool requestor_found = false;
		for(int i=0;i<requestor_vec.size();i+=1) {
			if(requestor_vec[i] == the_message->sender) {
				requestor_found = true;
				break;
			}
		}

		if(!requestor_found)
			requestor_vec.push_back(the_message->sender);
	} else if(the_message->l >= 4 && the_message->data[0] == 0x23 && the_message->data[1] == 0x60) { //Write a custom message.
		if(the_message->data[3] > 1)
			return;

		if(imid_next_source >= 0) {
			ai_cache_vec.push_back(*the_message);
			return;
		}
		
		const uint8_t space = the_message->data[2];
	
		String new_text = "";

		for(uint8_t i=0;i<space;i+=1)
			new_text += " ";

		for(uint8_t i=4;i<the_message->l;i+=1)
			new_text += char(the_message->data[i]);

		if(!writeIMIDTextMessage(new_text)) {
			imid_change_timer = 0;
			ai_cache_vec.push_back(*the_message);
		}
	} else if(the_message->l >= 3 && the_message->data[0] == 0x40 && the_message->data[1] == 0x10 && the_message->sender == ID_RADIO) { //Function change.
		const uint8_t source = the_message->data[2];
		bool set = false;

		ai_driver->setAllowStaggeredMulti((parameter_list->first_cd && source == ID_CDC) ||
												(parameter_list->first_tape && source == ID_TAPE) ||
												(parameter_list->first_xm && source == ID_XM));

		imid_next_subsource = -1;

		if(the_message->l >= 4) {
			const uint8_t subsource = the_message->data[3];
			imid_next_subsource = subsource;
			set = setIMIDSource(source, subsource);
		} else
			set = setIMIDSource(source, 0);

		if(!set) {
			imid_next_source = source;
			imid_change_timer = 0;
		}

		if(the_message->l >= 4 && source == ID_CDC && the_message->data[3] > 4) {
			uint8_t data_request_data[] = {0x60, 0x10};
			AIData data_request(sizeof(data_request_data), ID_IMID_SCR, ID_RADIO, data_request_data);

			ai_driver->writeAIData(&data_request, parameter_list->radio_connected);
		}
	} else if((the_message->data[0] == 0x39 || the_message->data[0] == 0x3B) && the_message->sender == ID_CDC) {
		if(the_message->l >= 8 && the_message->data[0] == 0x39) { //Track and disc.
			bool set = false;
			if(the_message->data[6] != disc)
				set = setIMIDSource(ID_CDC, 0);

			if(!set)
				imid_next_source = ID_CDC;
			
			ai_cd_mode = the_message->data[2];
			
			const uint8_t last_track = track, last_disc = disc;
			disc = the_message->data[6];
			track = the_message->data[7];
			
			const uint8_t cd_state = the_message->data[2];

			if(!writeIMIDCDCTrackMessage(disc, track, track_count, timer, getIECDStatus(ai_cd_mode), getIECDRepeat(ai_cd_mode))) {
				ai_cache_vec.push_back(*the_message);
				imid_change_timer = 0;
				return;
			}

			if(last_disc != disc || last_track != track) {
				if(!writeIMIDCDCTextMessage(1, "")) {
					ai_cache_vec.push_back(*the_message);
					imid_change_timer = 0;
					return;
				}

				if(!writeIMIDCDCTextMessage(2, ""))  {
					ai_cache_vec.push_back(*the_message);
					imid_change_timer = 0;
					return;
				}

				if(last_disc != disc) {
					if(!writeIMIDCDCTextMessage(0, ""))  {
						ai_cache_vec.push_back(*the_message);
						imid_change_timer = 0;
						return;
					}
				}
			}
		} else if(the_message->l >= 5 && the_message->data[0] == 0x3B) {
			timer = (the_message->data[3]<<8)|the_message->data[4];

			if(!writeIMIDCDCTrackMessage(disc, track, track_count, timer, getIECDStatus(ai_cd_mode), getIECDRepeat(ai_cd_mode))) {
				imid_change_timer = 0;
				ai_cache_vec.push_back(*the_message);
			}
		}
	} else if((the_message->sender == ID_CDC || the_message->sender == ID_CD) && the_message->l >= 2 && the_message->data[0] == 0x23) { //CD text message.
		uint8_t field = 0;

		switch(the_message->data[1]&0xF) {
			case 0x1: //Song title.
				field = 1;
				break;
			case 0x2: //Artist.
				field = 2;
				break;
			case 0x3: //Album.
				field = 0;
				break;
			default:
				return;
		}

		String text = "";
		for(int i=3;i<the_message->l;i+=1)
			text += char(the_message->data[i]);

		//TODO: Byte count.
		if(!writeIMIDCDCTextMessage(field, text)) {
			imid_change_timer = 0;
			ai_cache_vec.push_back(*the_message);
		}
	} else if(the_message->sender == ID_RADIO && the_message->l >= 6 && the_message->data[0] == 0x67) { //Frequency change message.	
		if(imid_next_source >= 0) {
			ai_cache_vec.push_back(*the_message);
			imid_change_timer = 0;
			return;
		}
		
		const uint16_t last_frequency = this->frequency;
		const uint16_t frequency = (the_message->data[1]<<8) | the_message->data[2];

		if(last_frequency != frequency)
			this->rds = false;

		/*if(frequency_change_timer_enabled && frequency_change_timer < 200) {
			this->frequency = frequency;
			this->decimal = the_message->data[3];
			this->preset = the_message->data[4]&0xF;
			this->stereo_mode = (the_message->data[4]&0xF0)>>4;

			if(frequency_change_timer > 150)
				frequency_change_timer = 150;
			frequency_change_timer_enabled = true;
			imid_change_timer = 0;
			return;
		}*/

		bool set = writeIMIDRadioMessage(frequency, the_message->data[3], the_message->data[4]&0xF, (the_message->data[4]&0xF0)>>4, false);
		imid_change_timer = 0;

		if(!set) {
			imid_change_timer = 0;
			ai_cache_vec.push_back(*the_message);
		} else {
			frequency_change_timer_enabled = true;
		}
	} else if(the_message->sender == ID_RADIO && the_message->l >= 2 && the_message->data[0] == 0x63) { //RDS.
		if(imid_next_source >= 0) {
			ai_cache_vec.push_back(*the_message);
			imid_change_timer = 0;
			return;
		}
		
		String rds_str = "";
		for(int i=2;i<the_message->l;i+=1)
			rds_str += char(the_message->data[i]);

		if(rds_str.equals(" ") || (rds_str.length() > 0 && rds_str[0] == 0x0))
			rds_str = "";
		
		if(the_message->data[1] == 0x61) { // True RDS.
			if(rds_str.length() > 0)
				this->rds = true;

			if(!writeIMIDRDSMessage(rds_str)) {
				imid_change_timer = 0;
				ai_cache_vec.push_back(*the_message);
			}
		} else if(the_message->data[1] == 0x60) { //Call sign.
			if(!writeIMIDCallsignMessage(rds_str)) {
				imid_change_timer = 0;
				ai_cache_vec.push_back(*the_message);
			}
		}
	} else if(the_message->sender == ID_RADIO && the_message->l >= 3 && the_message->data[0] == 0x62) { //Volume control display.
		if(!display_volume)
			return;

		if(imid_next_source >= 0) {
			ai_cache_vec.push_back(*the_message);
			imid_change_timer = 0;
			return;
		}
		
		const int max_vol = 40;
		const uint8_t new_vol = the_message->data[1]*max_vol/the_message->data[2];

		writeIMIDVolumeMessage(new_vol);
	} else if(the_message->sender == ID_XM && the_message->l >= 5 && the_message->data[0] == 0x39) { //XM channel change message.
		if(imid_next_source >= 0) {
			ai_cache_vec.push_back(*the_message);
			return;
		}
		
		const uint16_t channel = (the_message->data[2]<<8) | the_message->data[3];
		const uint8_t preset = the_message->data[4]&0x3F;

		if((the_message->data[4]&0xC0) == 0) {
			if(!writeIMIDSiriusNumberMessage(preset, channel, this->xm2)) {
				imid_change_timer = 0;
				ai_cache_vec.push_back(*the_message);
			}
		}
		//TODO: If signal is unavailable, send the appropriate message.
	} else if(the_message->sender == ID_XM && the_message->l >= 2 && the_message->data[0] == 0x23) { //Sirius text message.
		if(imid_next_source >= 0) {
			ai_cache_vec.push_back(*the_message);
			imid_change_timer = 0;
			return;
		}
		
		uint8_t field = 0;
		switch(the_message->data[1]&0xF) {
			case 1:
				field = 2;
				break;
			case 2:
				field = 1;
				break;
			case 3:
				field = 0;
				break;
			case 4:
				field = 3;
				break;
			default:
				return;
		}

		String text = "";
		for(unsigned int i=3;i<the_message->l;i+=1)
			text += char(the_message->data[i]);

		if(!writeIMIDSiriusTextMessage(field, text)) {
			imid_change_timer = 0;
			ai_cache_vec.push_back(*the_message);
		}
	} else if((the_message->sender == ID_PHONE || the_message->sender == ID_ANDROID_AUTO) && the_message->l >= 5 && the_message->data[0] == 0x3B) { //Bluetooth timer.
		if(imid_next_source >= 0) {
			ai_cache_vec.push_back(*the_message);
			imid_change_timer = 0;
			return;
		}
		
		const long time = the_message->data[4] | (the_message->data[3]<<8);
		if(!setBTTimer(time)) {
			ai_cache_vec.push_back(*the_message);
			imid_change_timer = 0;
		}
	} else if(the_message->sender == ID_PHONE && the_message->l >= 3 && the_message->data[0] == 0x23 && (the_message->data[1]&0xF0) == 0x60) { //Bluetooth text message.	
		if(imid_next_source >= 0) {
			ai_cache_vec.push_back(*the_message);
			imid_change_timer = 0;
			return;
		}
		
		uint8_t leader = 0xFF;

		switch(the_message->data[1]) {
		case 0x61:
			leader = 0x42;
			break;
		case 0x62:
			leader = 0x43;
			break;
		case 0x63:
			leader = 0x44;
			break;
		case 0x64:
			leader = 0x41;
			break;
		default:
			return;
		}

		String sent_text = "";
		for(int i=3;i<the_message->l;i+=1)
			sent_text += char(the_message->data[i]);

		if(!this->setBTText(leader, sent_text)) {
			imid_change_timer = 0;
			ai_cache_vec.push_back(*the_message);
		}
	} else if(the_message->sender == ID_ANDROID_AUTO && the_message->l >= 2 && the_message->data[0] == 0x30 && the_message->data[1] == 0x0) { //Phone disconnected.
		if(imid_next_source >= 0) {
			ai_cache_vec.push_back(*the_message);
			imid_change_timer = 0;
			return;
		}
		
		if(!this->setBTModeNotConnected()) {
			imid_change_timer = 0;
			ai_cache_vec.push_back(*the_message);
			return;
		}
	} else if(the_message->sender == ID_ANDROID_AUTO && the_message-> l >= 2 && the_message->data[0] == 0x23 && (the_message->data[1]&0xF0) == 0x60) { //Mirror text message.
		if(imid_next_source >= 0) {
			ai_cache_vec.push_back(*the_message);
			imid_change_timer = 0;
			return;
		}
		
		uint8_t leader = 0xFF;

		switch(the_message->data[1]) {
		case 0x61:
			leader = 0x42;
			break;
		case 0x62:
			leader = 0x43;
			break;
		case 0x63:
			leader = 0x44;
			break;
		case 0x64:
			leader = 0x45;
			break;
		default:
			return;
		}

		String sent_text = "";
		for(int i=2;i<the_message->l;i+=1)
			sent_text += char(the_message->data[i]);

		if(sent_text.length() >= 0 || leader != 0x45) {
			if(!this->setBTText(leader, sent_text)) {
				imid_change_timer = 0;
				ai_cache_vec.push_back(*the_message);
				return;
			}
		} else {
			
		}
	} else if(the_message->sender == ID_NAV_COMPUTER && the_message->l >= 2 && the_message->data[0] == 0x2B) { //Menu message.
		const uint8_t operation = the_message->data[1];

		if(operation == 0x55 || operation == 0x56 || operation == 0x57) { //Menu presence request.
			String menu_requested = "";
			for(int i=2;i<the_message->l;i+=1)
				menu_requested += char(the_message->data[i]);

			menu_requested.trim();

			if(menu_requested.equalsIgnoreCase("SETTING")) {
				const MenuList settings_menu = getMenu(MENU_INDEX_IMID_SETTINGS, parameter_list->locale);
				const String menu_name = settings_menu.title;

				if(operation == 0x55) //Display the menu.
					createIMIDSettingsMenu();
				else {
					uint8_t response_data[] = {0x2B, operation};
					AIData response_msg(sizeof(response_data) + (operation == 0x57 ? menu_name.length() : 0), ID_IMID_SCR, the_message->sender);

					for(int i=0;i<sizeof(response_data);i+=1)
						response_msg[i] = response_data[i];

					if(operation == 0x57) {
						for(int i=0;i<menu_name.length() && i+sizeof(response_data)<response_msg.l;i+=1)
							response_msg[i+sizeof(response_data)] = uint8_t(menu_name[i]);
					}

					ai_driver->writeAIData(&response_msg);
				}
			}
		} else if(operation == 0x45) { //Menu request.
			createIMIDSettingsMenu();
		} else if(operation == 0x40) { //Menu closed.
			if(*active_menu == MENU_IMID) {
				*active_menu = 0;

				uint8_t close_data[] = {0x2B, 0x40};
				AIData close_msg(sizeof(close_data), ID_IMID_SCR, the_message->sender, close_data);
				ai_driver->writeAIData(&close_msg);
			} else if(*active_menu == MENU_IMID_CHARACTER) {
				createIMIDSettingsMenu();
			}
		} else if(operation == 0x60) { //Selection.
			const int selected = the_message->data[2] - 1;
			if(selected < 0)
				return;

			if(*active_menu == MENU_IMID) {
				const MenuList settings_menu = getMenu(MENU_INDEX_IMID_SETTINGS, parameter_list->locale);
				switch(settings_menu.getGlobalIndex(selected)) {
				case MENU_INDEX_IMID_SETTINGS_RDS:
					display_rds = !display_rds;
					createIMIDSettingsMenuOption(selected);

					if((imid_mode&0xFF) == ID_RADIO)
						writeIMIDRadioMessage(frequency, decimal, preset, stereo_mode);
					
					setting_changed = true;
					break;
				case MENU_INDEX_IMID_SETTINGS_CD_TEXT:
					if(parameter_list->imid_cd_text != nullptr && parameter_list->imid_cd_text != NULL) {
						*parameter_list->imid_cd_text = !*parameter_list->imid_cd_text;
						parameter_list->cd_text_changed = true;
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
